bitaxeorg/BitaxeGammaHex/3d/TSOT-23-5_RIT.step

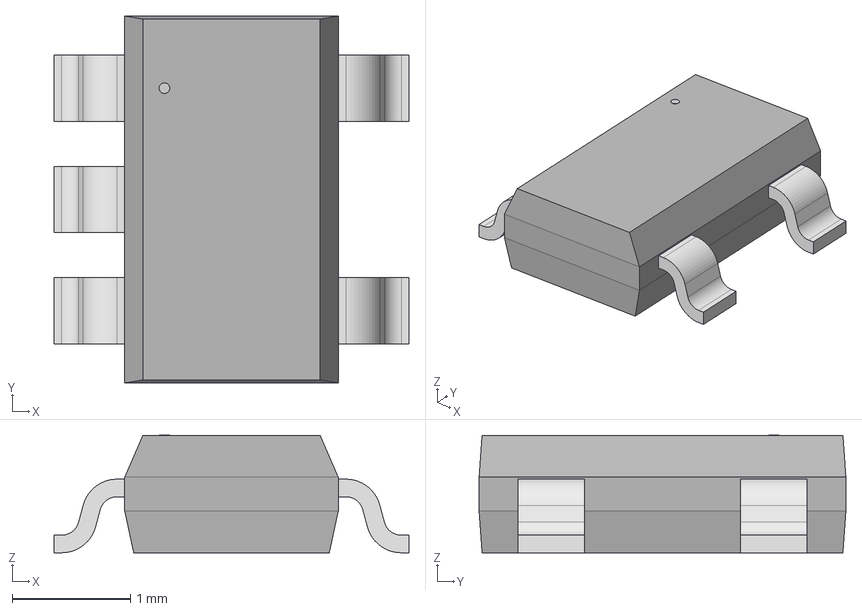
[picture p17: CAD file, 2026-07-20]
3d/TSOT-23-5_RIT.step
3.00 x 3.10 x 0.993 mm
