bitaxeorg/BitaxeGammaHex/3d/DRC0010J.stp

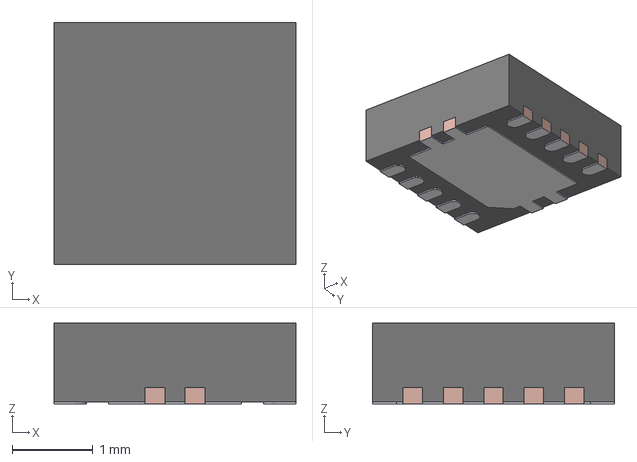
[picture p18: CAD file, 2026-07-20]
3d/DRC0010J.stp
3.00 x 3.00 x 1.00 mm
BODY-SON
FRAME-DRC0010J
