bitaxeorg/BitaxeGammaHex/3d/XTAL_SC32S-7PF20PPM_EPS.step

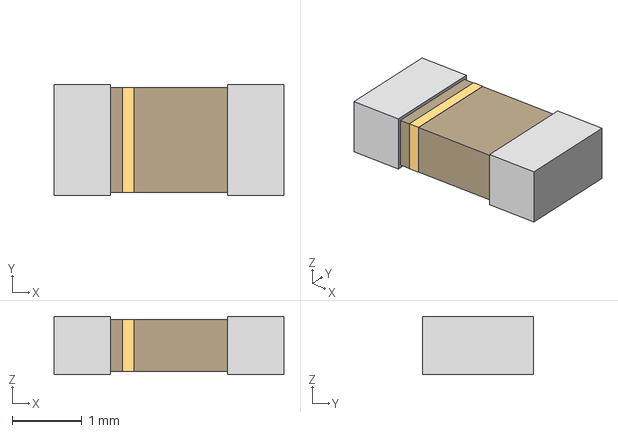
[picture p19: CAD file, 2026-07-20]
3d/XTAL_SC32S-7PF20PPM_EPS.step
3.30 x 1.60 x 0.838 mm
