bitaxeorg/BitaxeGammaHex/3d/BQB0016A.stp

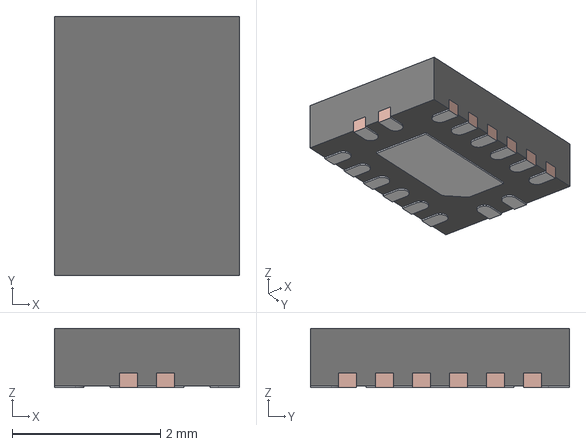
[picture p20: CAD file, 2026-07-20]
3d/BQB0016A.stp
2.50 x 3.50 x 0.8 mm
FRAME
