bitaxeorg/BitaxeGammaHex/3d/SOT-23-5_M5_MCH.step

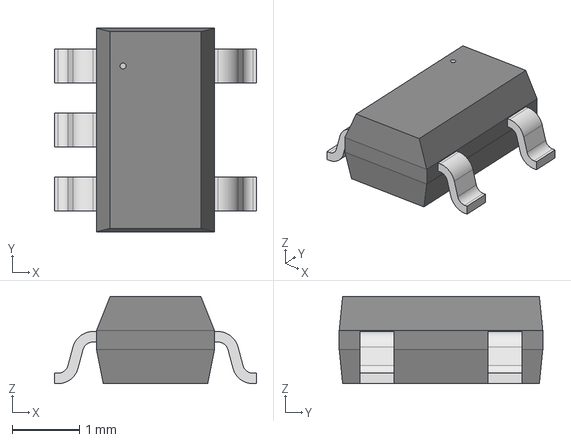
[picture p22: CAD file, 2026-07-20]
3d/SOT-23-5_M5_MCH.step
3.00 x 3.02 x 1.30 mm
