bitaxeorg/BitaxeGammaHex/3d/Bitaxe_Heatsink.step

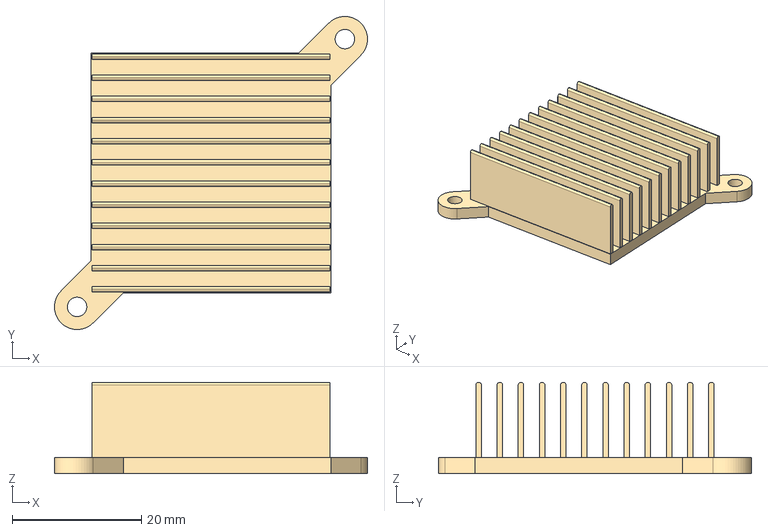
[picture p24: CAD file, 2026-07-20]
3d/Bitaxe_Heatsink.step
48.4 x 48.4 x 14.1 mm
