bitaxeorg/BitaxeGammaHex/3d/oscillator3.2x2.5.step

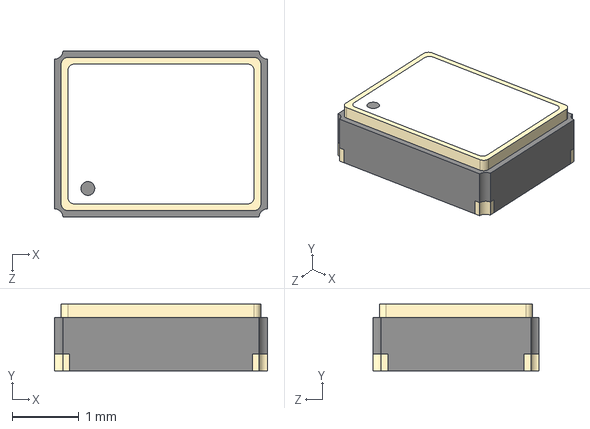
[picture p25: CAD file, 2026-07-20]
3d/oscillator3.2x2.5.step
3.20 x 1.00 x 2.50 mm
