bitaxeorg/BitaxeGammaHex/3d/c-63862-1-r-3d.stp

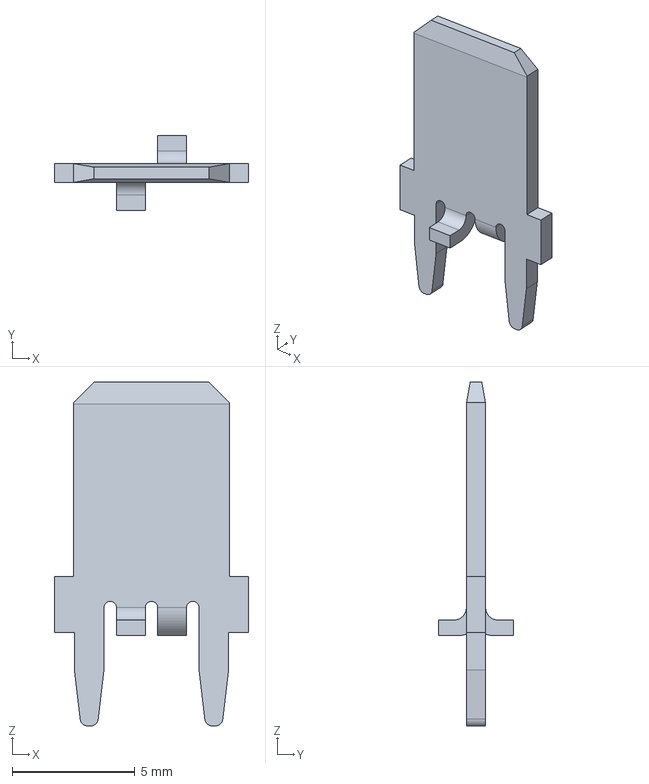
[picture p26: CAD file, 2026-07-20]
3d/c-63862-1-r-3d.stp
7.92 x 3.07 x 14.0 mm
