bitaxeorg/BitaxeGammaHex/3d/CS1213AG-tr.stp

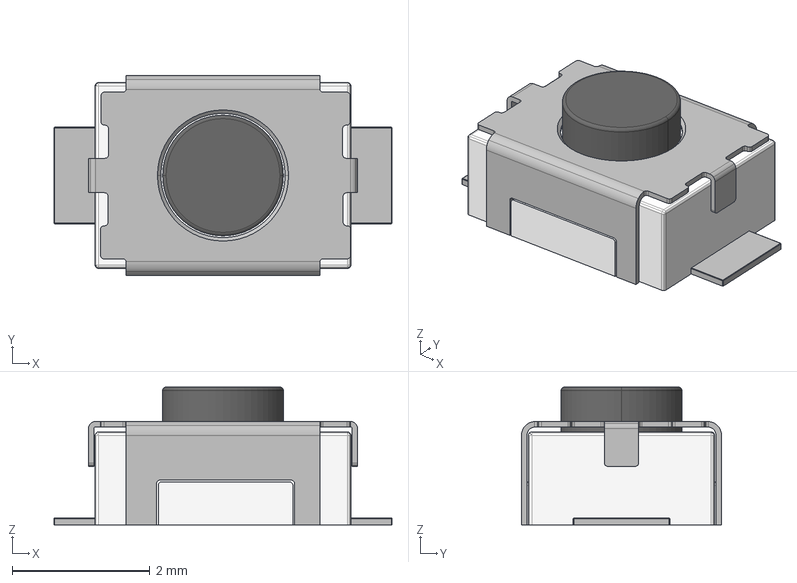
[picture p28: CAD file, 2026-07-20]
3d/CS1213AG-tr.stp
4.90 x 2.90 x 2.00 mm
