bitaxeorg/BitaxeGammaHex/3d/lga115x.step

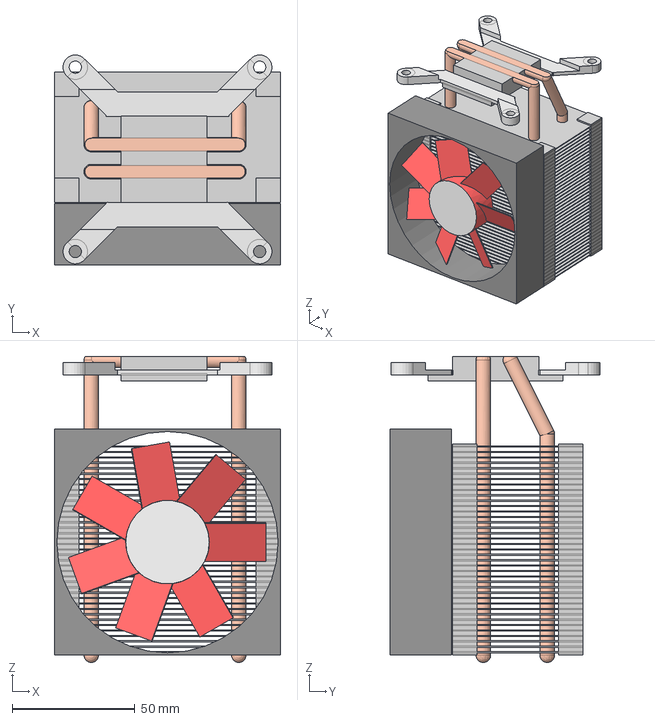
[picture p29: CAD file, 2026-07-20]
3d/lga115x.step
92.0 x 85.5 x 124.5 mm
