bitaxeorg/BitaxeGammaHex/3d/OLED_0.91_128x32.stp

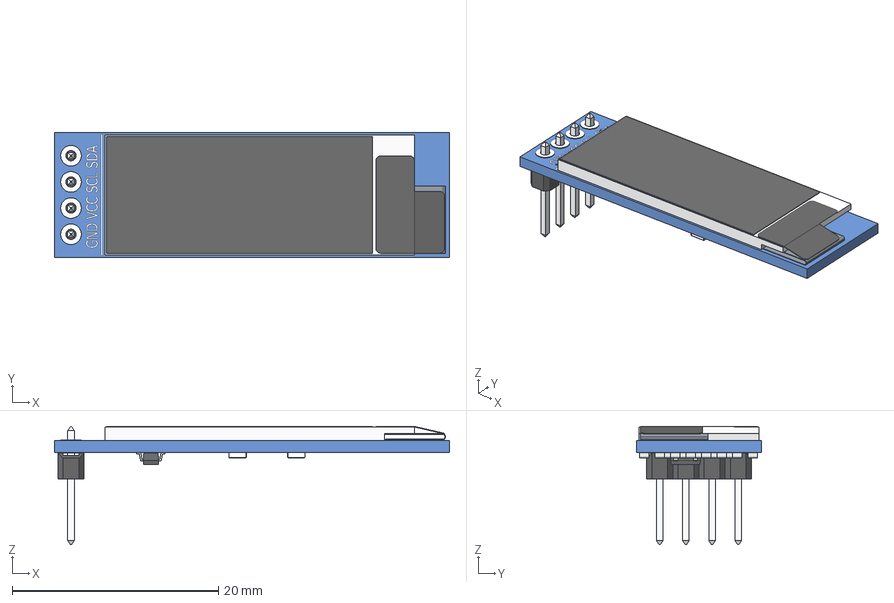
[picture p30: CAD file, 2026-07-20]
3d/OLED_0.91_128x32.stp
38.3 x 12.1 x 11.5 mm
OLED_0.91_128x32
Pin Header 4 x 1 TH 2.54mm Pitch
RESC-0603 x 13
2SD0601A
