bitaxeorg/BitaxeGammaHex/3d/CX3225SB16000H0FLJCC.STEP

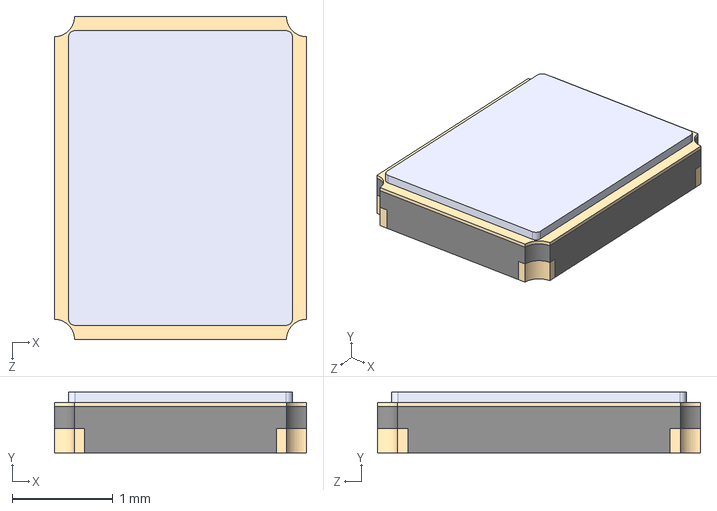
[picture p31: CAD file, 2026-07-20]
3d/CX3225SB16000H0FLJCC.STEP
2.50 x 0.6 x 3.20 mm
