bitaxeorg/BitaxeGammaHex/3d/bm1366.step

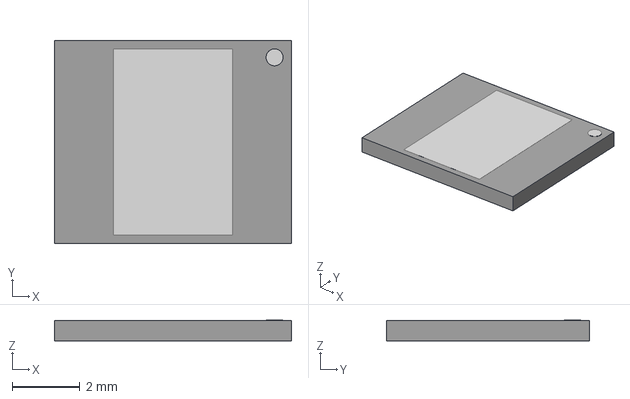
[picture p32: CAD file, 2026-07-20]
3d/bm1366.step
7.00 x 6.00 x 0.61 mm
