bitaxeorg/BitaxeGammaHex/3d/barrel-jack.step

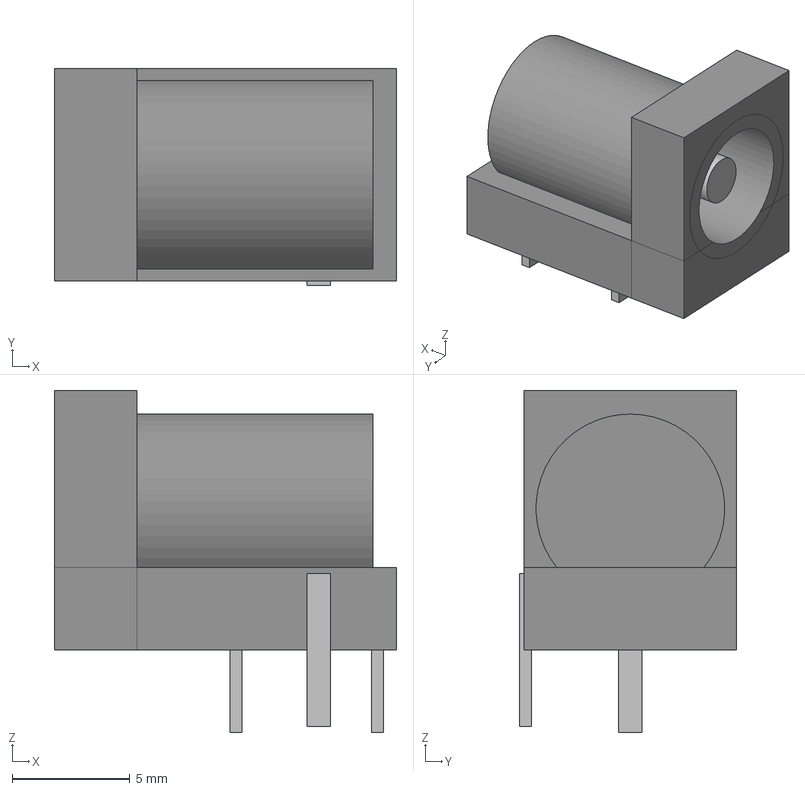
[picture p33: CAD file, 2026-07-20]
3d/barrel-jack.step
14.5 x 9.20 x 14.5 mm
