bitaxeorg/BitaxeGammaHex/3d/SN74AXC1T45DBVR.STEP

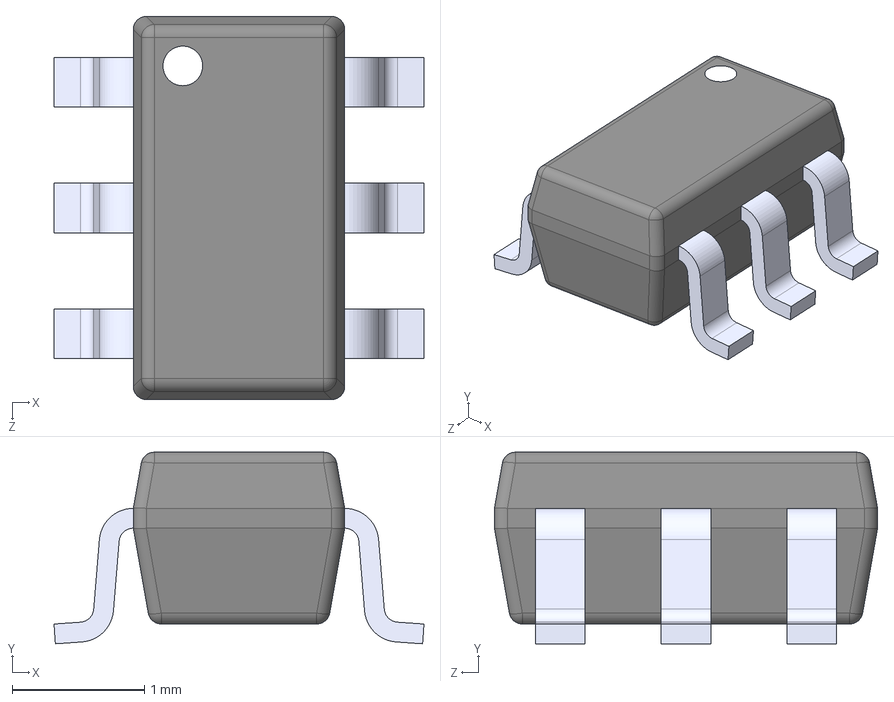
[picture p34: CAD file, 2026-07-20]
3d/SN74AXC1T45DBVR.STEP
2.80 x 1.45 x 2.90 mm
