bitaxeorg/BitaxeGammaHex/3d/heatsink-13x12x5.step

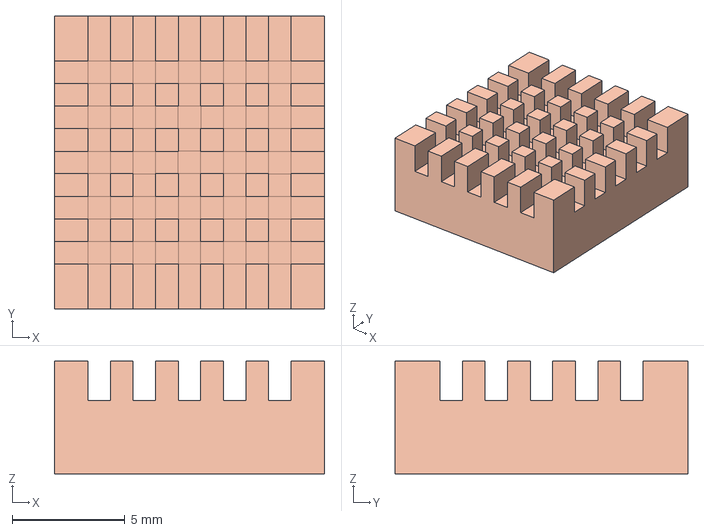
[picture p37: CAD file, 2026-07-20]
3d/heatsink-13x12x5.step
12.0 x 13.0 x 5.00 mm
