bitaxeorg/BitaxeGammaHex/3d/KMR231GLFS.stp

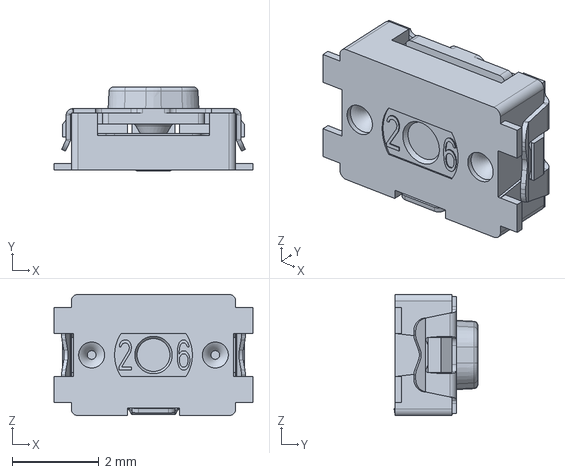
[picture p38: CAD file, 2026-07-20]
3d/KMR231GLFS.stp
4.60 x 1.94 x 2.80 mm
