bitaxeorg/BitaxeGammaHex/3d/21-0164B_L622-1_MXM.step

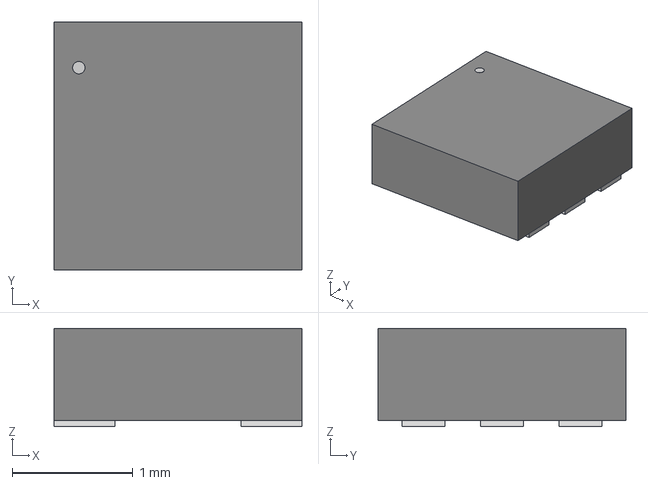
[picture p40: CAD file, 2026-07-20]
3d/21-0164B_L622-1_MXM.step
2.06 x 2.06 x 0.815 mm
