bitaxeorg/BitaxeGammaHex/3d/CUI_DEVICES_PJ-002AH.step

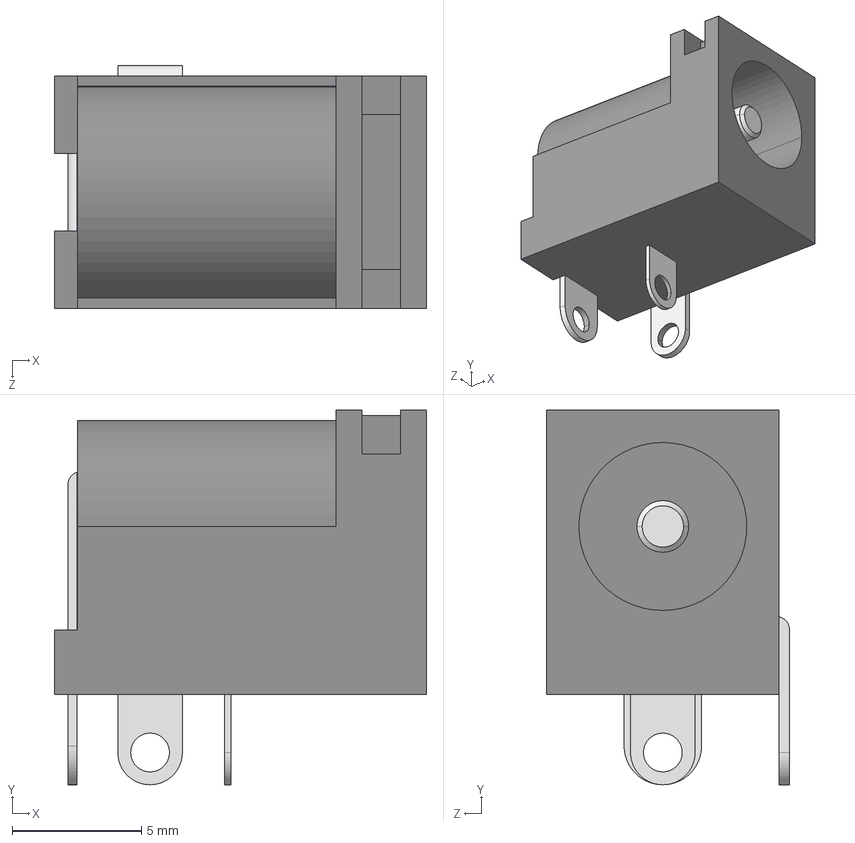
[picture p42: CAD file, 2026-07-20]
3d/CUI_DEVICES_PJ-002AH.step
14.4 x 14.5 x 9.40 mm
