bitaxeorg/BitaxeGammaHex/3d/CUI_DEVICES_PJ-037AH.step

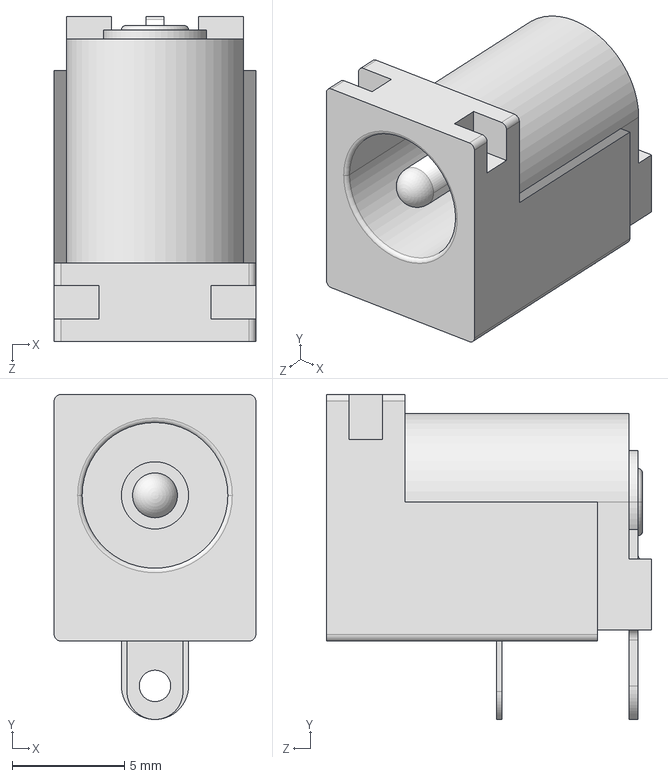
[picture p43: CAD file, 2026-07-20]
3d/CUI_DEVICES_PJ-037AH.step
9.00 x 14.5 x 14.5 mm
