bitaxeorg/BitaxeGammaHex/3d/SMV_z90.stp

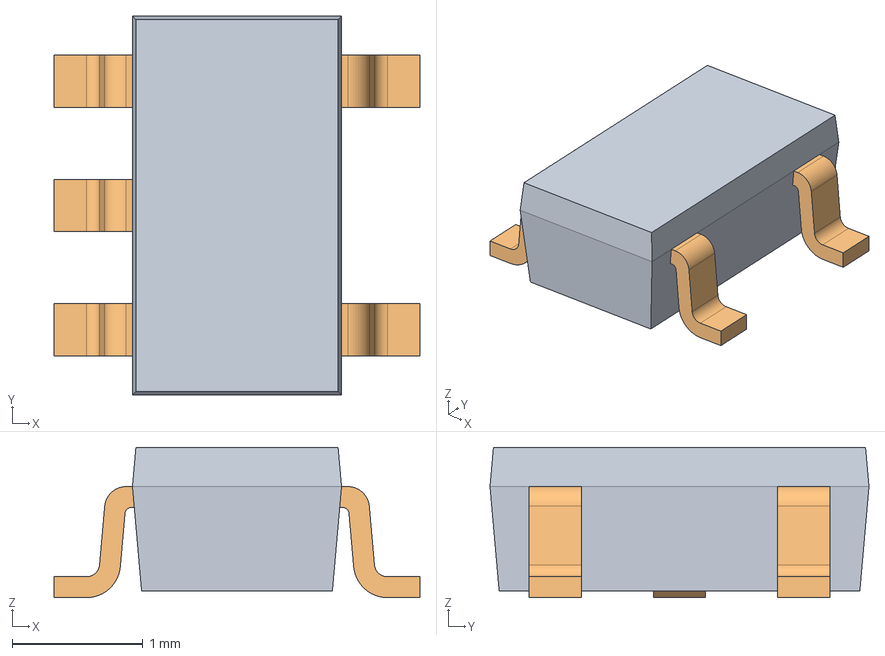
[picture p45: CAD file, 2026-07-20]
3d/SMV_z90.stp
2.80 x 2.90 x 1.15 mm
