bitaxeorg/BitaxeGammaHex/3d/XRCGB27M120F3M10R0_MUR.step

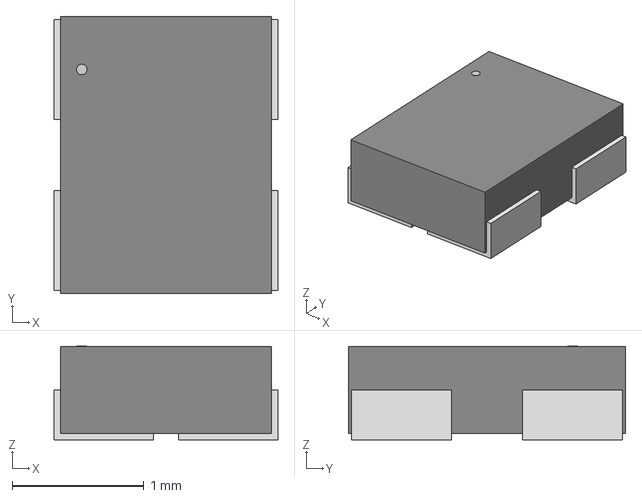
[picture p46: CAD file, 2026-07-20]
3d/XRCGB27M120F3M10R0_MUR.step
1.70 x 2.11 x 0.714 mm
