bitaxeorg/BitaxeGammaHex/3d/XT30PW-M.stp

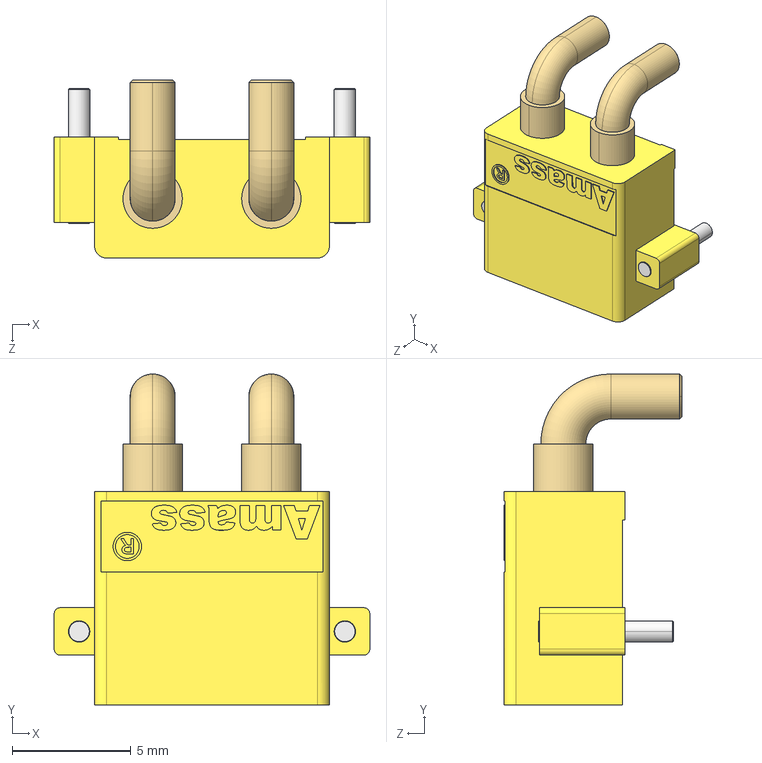
[picture p48: CAD file, 2026-07-20]
3d/XT30PW-M.stp
13.3 x 13.9 x 7.50 mm
