bitaxeorg/BitaxeGammaHex/3d/bm1370.step

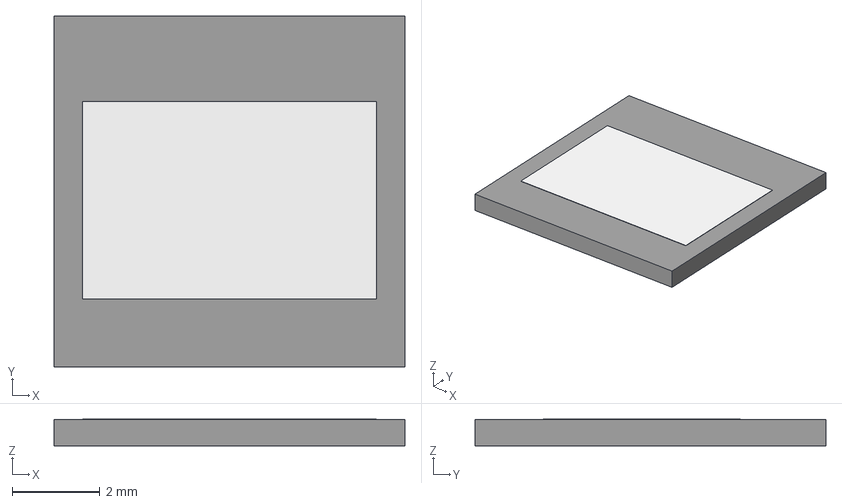
[picture p49: CAD file, 2026-07-20]
3d/bm1370.step
8.00 x 8.00 x 0.61 mm
