bitaxeorg/BitaxeGammaHex/3d/DCJ250-20-B-XX-X_REVA1.step

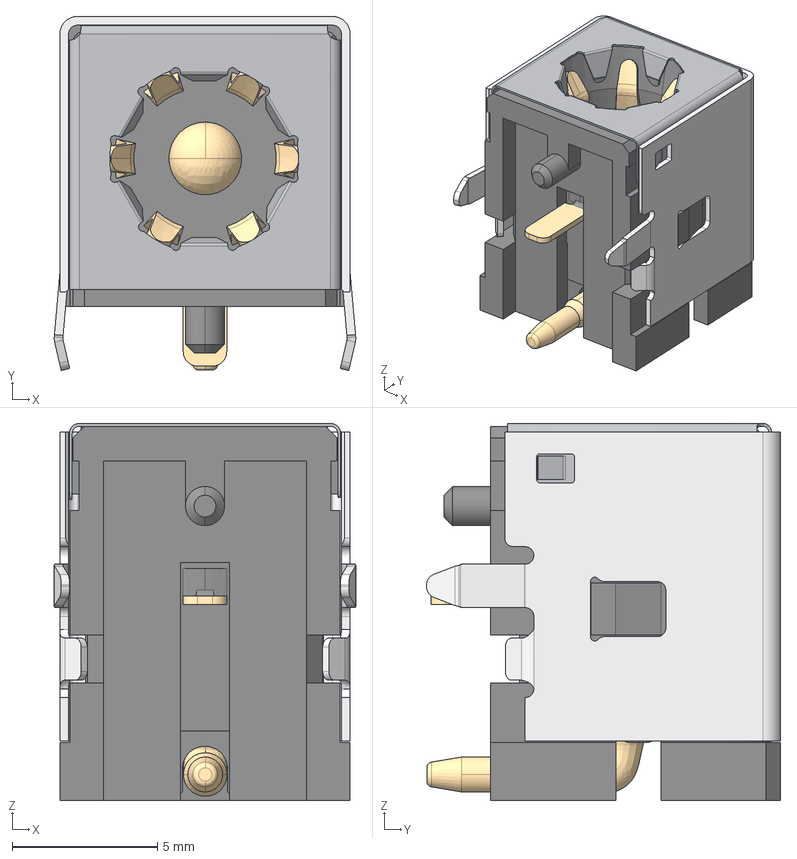
[picture p51: CAD file, 2026-07-20]
3d/DCJ250-20-B-XX-X_REVA1.step
10.4 x 12.2 x 13.0 mm
