bitaxeorg/BitaxeGammaHex/3d/SIS0011A.stp

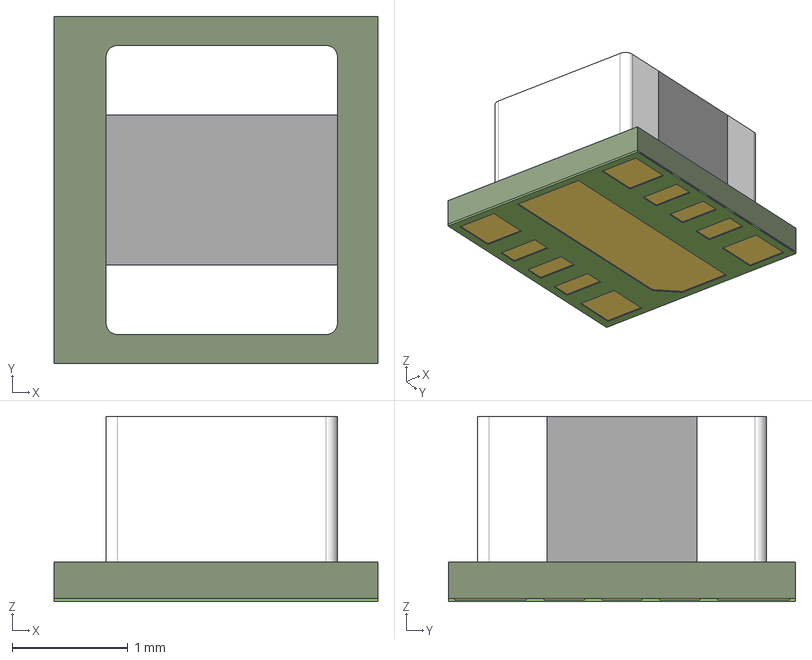
[picture p52: CAD file, 2026-07-20]
3d/SIS0011A.stp
2.80 x 3.00 x 1.60 mm
SOLDERMASK-SIS0011A
METAL-SIS0011A
SUBSTRATE-SIP
INDUCTOR-BODY-MLV
INDUCTOR-TERMNL-MLV x 2
