bitaxeorg/BitaxeGammaHex/3d/PLCC6_LED_3_5X3_4X2_8_CRW.step

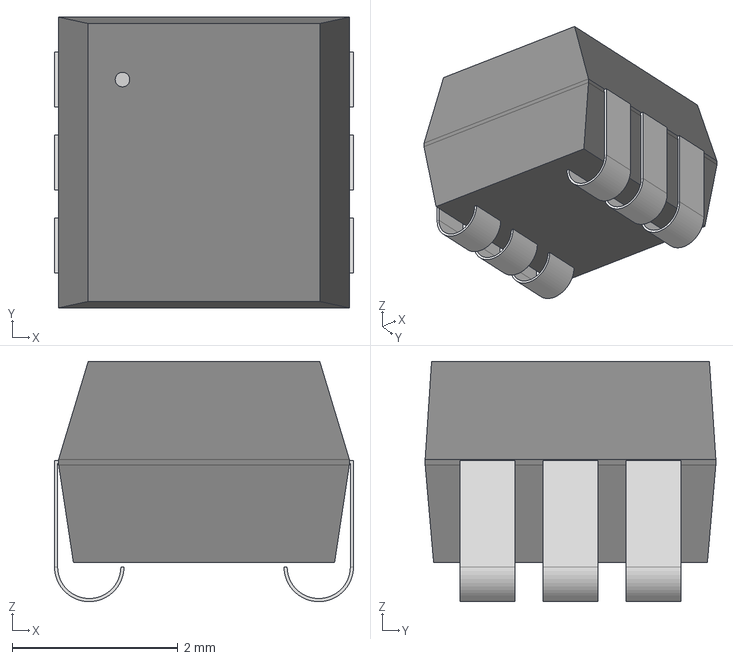
[picture p53: CAD file, 2026-07-20]
3d/PLCC6_LED_3_5X3_4X2_8_CRW.step
3.61 x 3.51 x 2.90 mm
