bitaxeorg/BitaxeGammaHex/3d/SW_CS1213AGF260_CRS.step

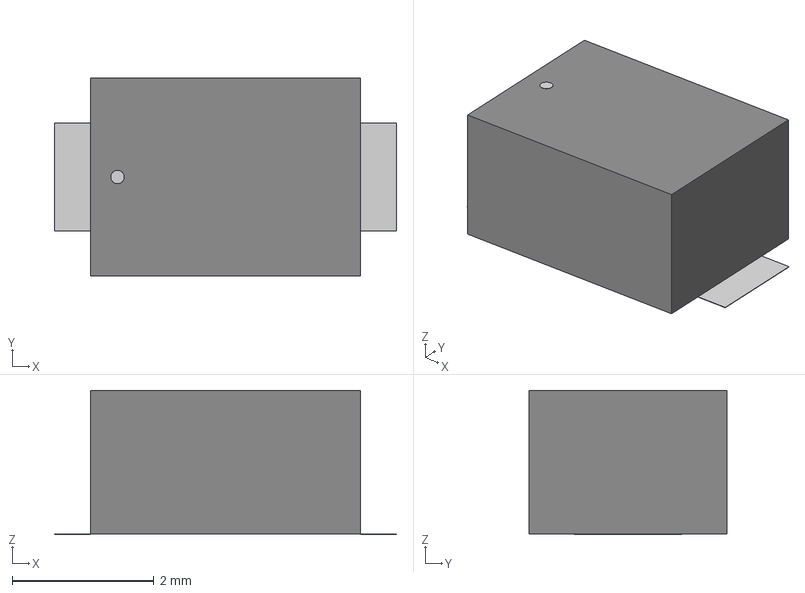
[picture p54: CAD file, 2026-07-20]
3d/SW_CS1213AGF260_CRS.step
4.83 x 2.79 x 2.04 mm
