bitaxeorg/BitaxeGammaHex/3d/Coilcraft-SLC1175.STEP

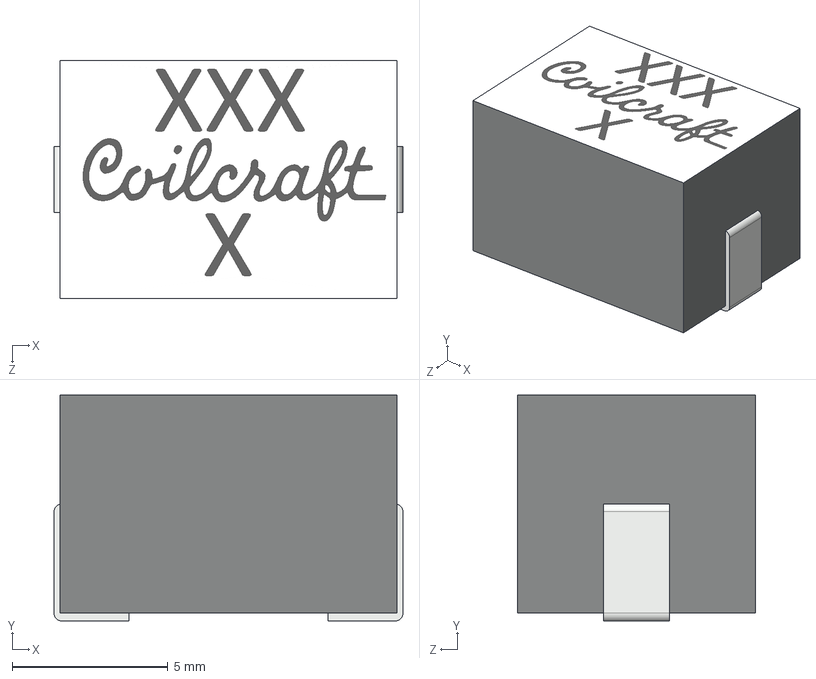
[picture p55: CAD file, 2026-07-20]
3d/Coilcraft-SLC1175.STEP
11.2 x 7.25 x 7.65 mm
