bitaxeorg/BitaxeGammaHex/BitaxeGammaHex.kicad_sch

## KiCad design BitaxeGammaHex.kicad_sch (2026-07-27)

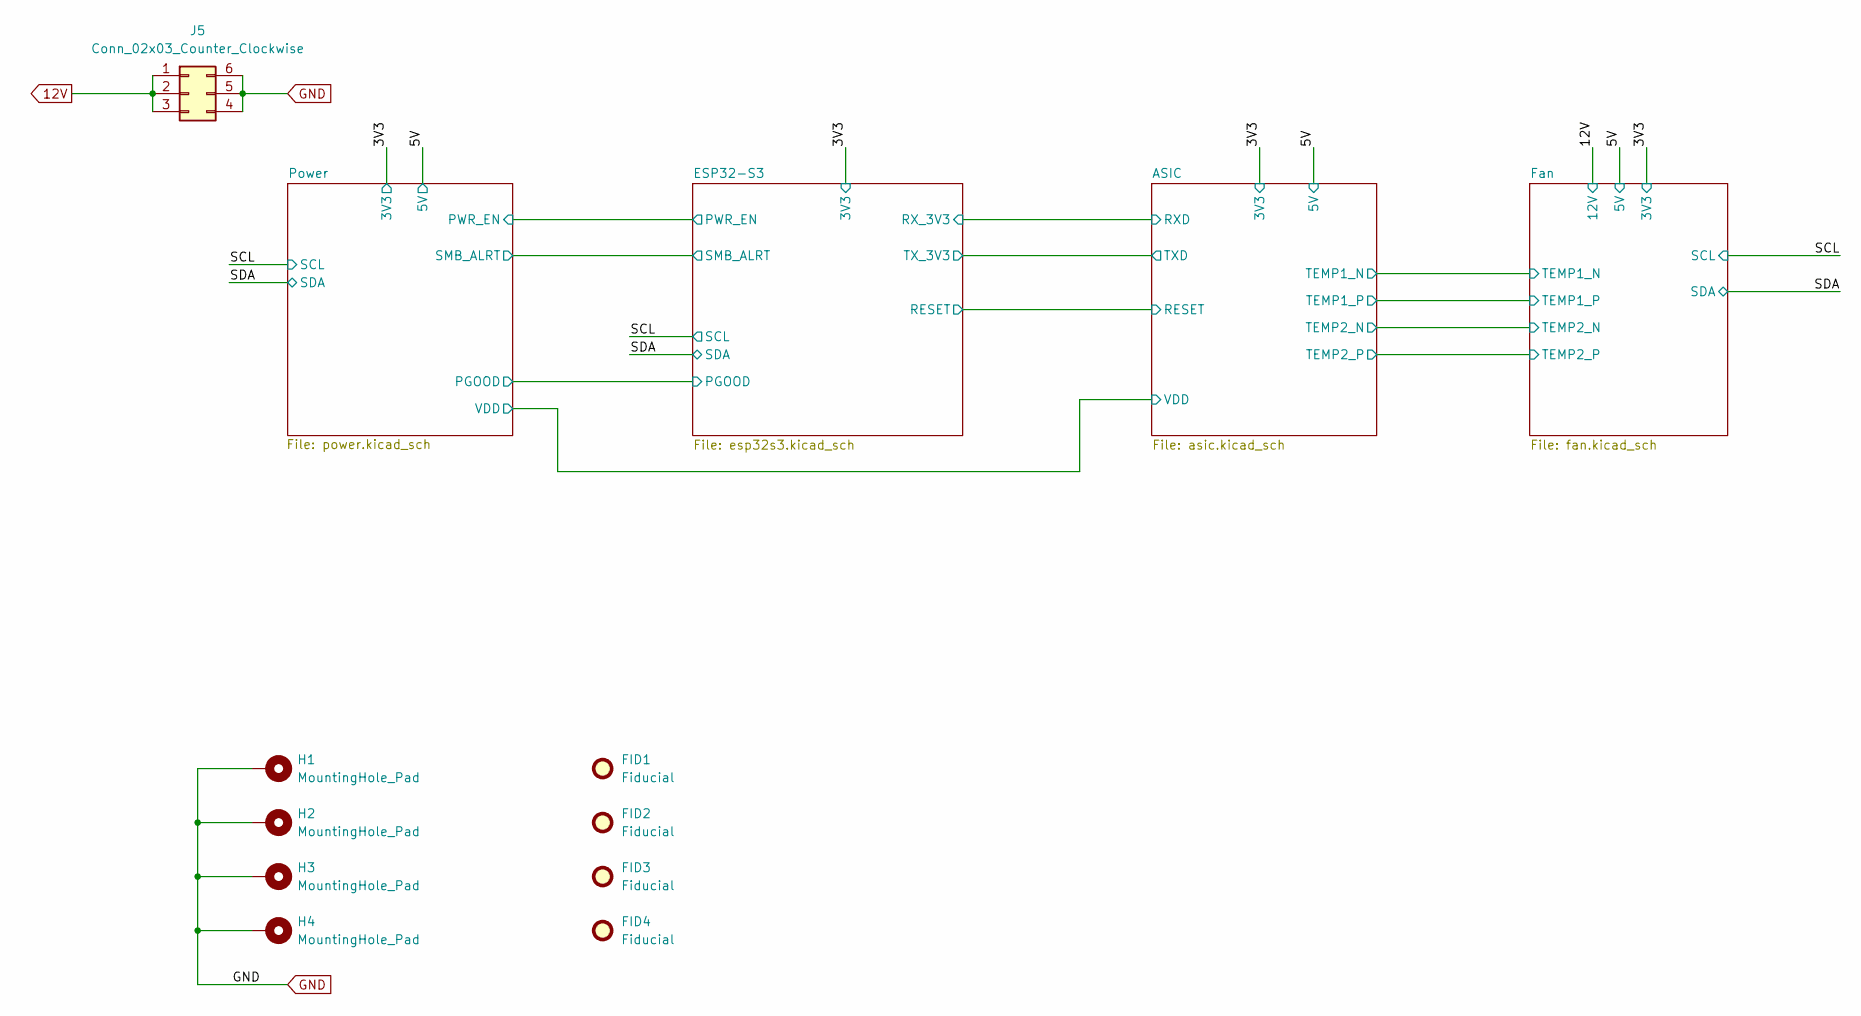
[picture p56: schematic BitaxeGammaHex.kicad_sch]

Parts:
FID1, FID2, FID3, FID4: Fiducial; Fiducial_1mm_Mask2mm
H1, H2, H3, H4: MountingHole_Pad; MountingHole_3.2mm_M3_Pad_Via
J5: Conn_02x03_Counter_Clockwise; MOLEX 39301060

Connections:
12V: J5.1, J5.2, J5.3
GND: H1.1, H2.1, H3.1, H4.1, J5.4, J5.5, J5.6
