bitaxeorg/BitaxeGammaHex/asic.kicad_sch

## KiCad design asic.kicad_sch (2026-07-27)

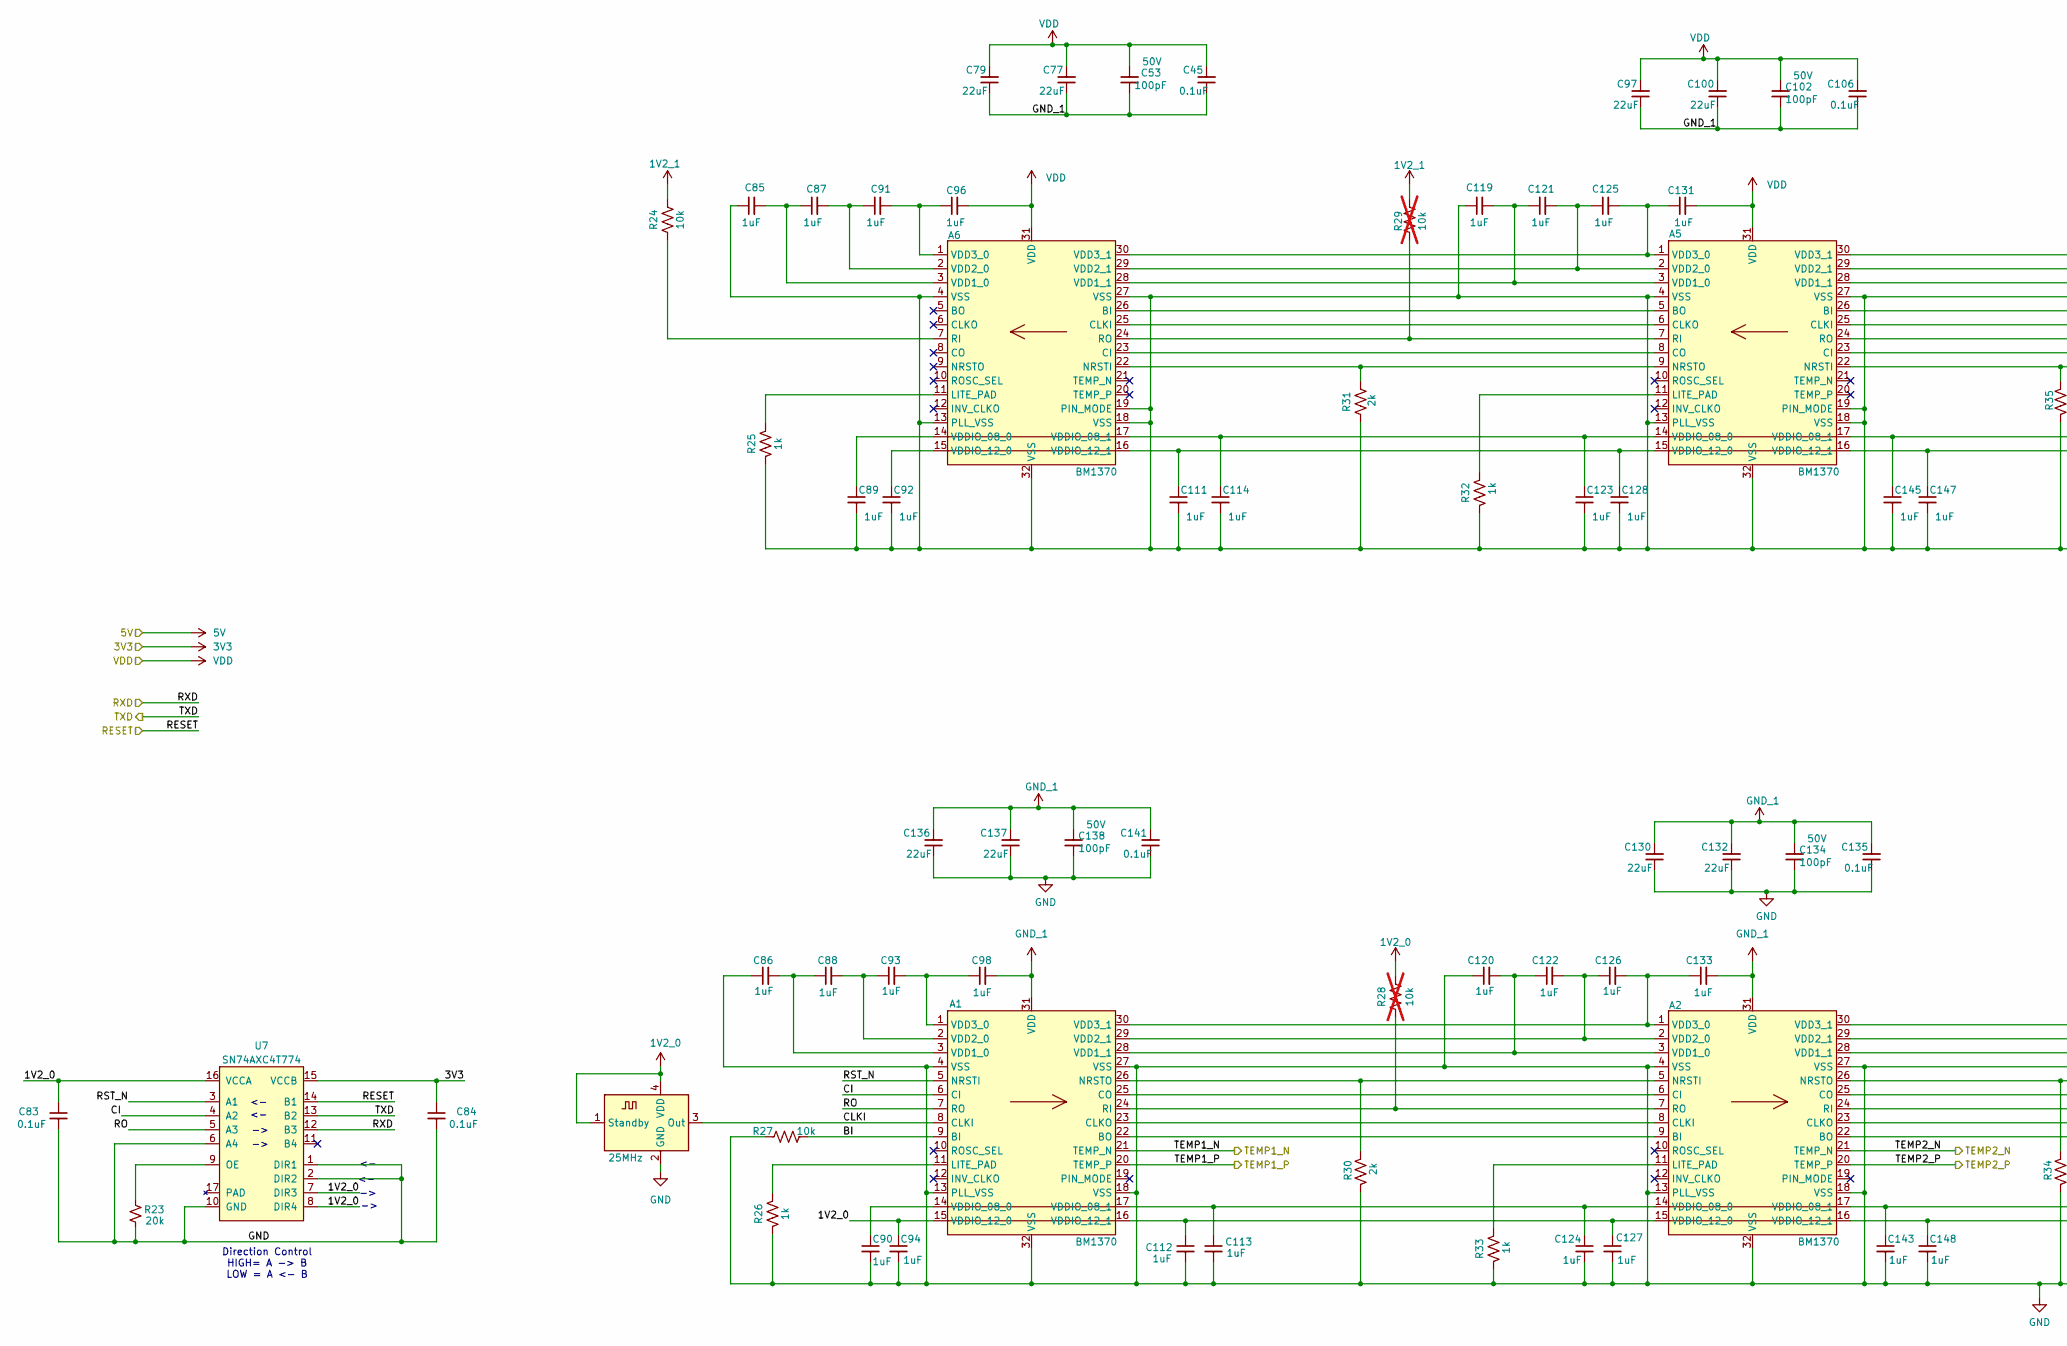
[picture p57: schematic asic.kicad_sch, part in row 1, column 1]

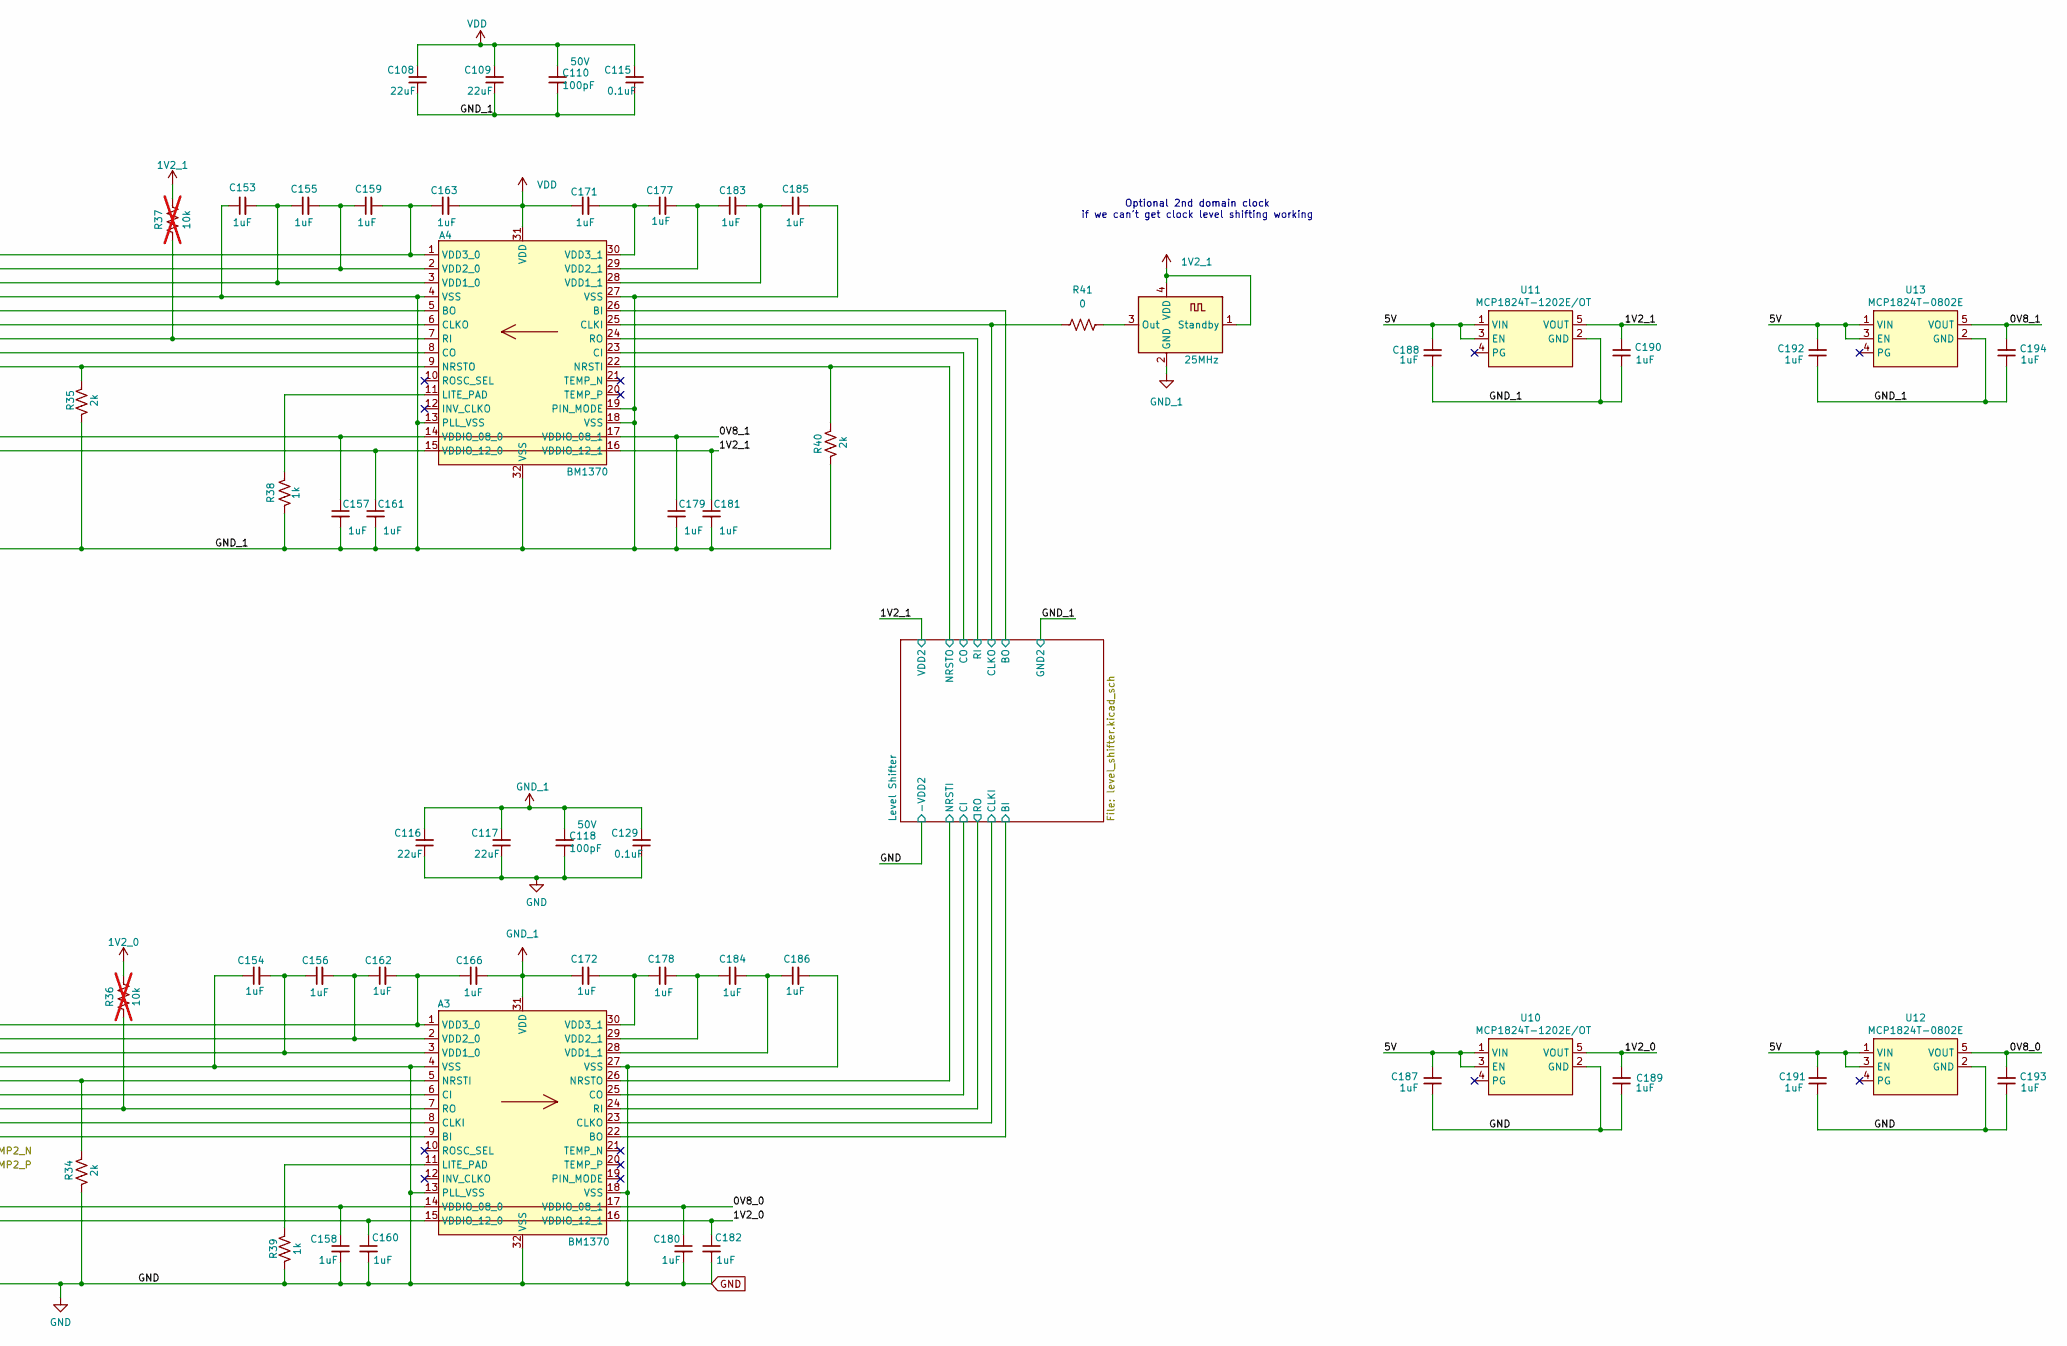
[picture p58: schematic asic.kicad_sch, part in row 1, column 2]

Parts:
A1, A2, A3, A4, A5, A6: BM1370; PARTNO BM1370
C45, C106, C115, C129, C135, C141: 0.1uF; C_0402_1005Metric; PARTNO GRM188R61E106KA73D
C53, C102, C110, C118, C134, C138: 100pF; C_0402_1005Metric; Voltage 50V; PARTNO CC0402JRNPO9BN101
C77, C79, C97, C100, C108, C109, C116, C117, C130, C132, C136, C137: 22uF; C_0805_2012Metric; PARTNO CL21A226MAQNNNE
C83, C84: 0.1uF; C_0402_1005Metric; PARTNO KGM05AR71C104KH
C85, C86, C87, C88, C89, C90, C91, C92, C93, C94, C96, C98, C111, C112, C113, C114, C119, C120, C121, C122, C123, C124, C125, C126, C127, C128, C131, C133, C143, C145, C147, C148, C153, C154, C155, C156, C157, C158, C159, C160, C161, C162, C163, C166, C171, C172, C177, C178, C179, C180, C181, C182, C183, C184, C185, C186: 1uF; C_0402_1005Metric; PARTNO CL05A105KO5NNNC; LCSC C29266
C187, C188, C189, C190, C191, C192, C193, C194: 1uF; C_0402_1005Metric; PARTNO CL05A105KO5NNNC
R23: 20k; R_0402_1005Metric; PARTNO RC0402FR-0720KL
R24, R27: 10k; R_0402_1005Metric; PARTNO RC0402DR-0710KL; LCSC C471764
R25, R26, R32, R33, R38, R39: 1k; R_0402_1005Metric; PARTNO RC0402FR-071KL; LCSC C106235
R28, R29, R36, R37: 10k; R_0402_1005Metric; PARTNO RC0402DR-0710KL; LCSC C471764; not fitted
R30, R31, R34, R35, R40: 2k; R_0402_1005Metric; PARTNO RC0402FR-072KL; LCSC C60488
R41: 0; R_0402_1005Metric; PARTNO RC0402JR-070RL
U7: SN74AXC4T774; TSSOP-16_4.4x5mm_P0.65mm; PARTNO SN74AXC4T774PWR
U8, U9: 25MHz; Oscillator_SMD_EuroQuartz_XO32-4Pin_3.2x2.5mm; PARTNO SX3M25.000E20F30THN
U10, U11: MCP1824T-1202E/OT; SOT-23-5; PARTNO MCP1824T-1202E/OT
U12, U13: MCP1824T-0802E; SOT-23-5; PARTNO MCP1824T-0802E/OT

Connections:
0V8_0: A3.17 (VDDIO_08_1), C180.1, C193.2, U12.5 (VOUT)
0V8_1: A4.17 (VDDIO_08_1), C179.1, C194.2, U13.5 (VOUT)
1V2_0: A1.15 (VDDIO_12_0), A3.16 (VDDIO_12_1), C83.1, C94.1, C182.1, C189.2, R28.2, R36.2, U7.7 (DIR3), U7.8 (DIR4), U7.16 (VCCA), U8.1 (Standby), U8.4 (VDD), U10.5 (VOUT)
1V2_1: A4.16 (VDDIO_12_1), C181.1, C190.2, R24.2, R29.2, R37.2, U9.1 (Standby), U9.4 (VDD), U11.5 (VOUT)
3V3: C84.1, U7.15 (VCCB)
5V: C187.2, C188.2, C191.2, C192.2, U10.1 (VIN), U10.3 (EN), U11.1 (VIN), U11.3 (EN), U12.1 (VIN), U12.3 (EN), U13.1 (VIN), U13.3 (EN)
BI: A1.9 (BI), A3.22 (BO), R27.2
BO: A4.26 (BI)
CI: A1.6 (CI), A3.25 (CO), U7.4 (A2)
CLKI: A1.8 (CLKI), A3.23 (CLKO), U8.3 (Out)
CLKO: A4.25 (CLKI), R41.1
CO: A4.23 (CI)
GND: A1.4 (VSS), A1.13 (PLL_VSS), A1.18 (VSS), A1.27 (VSS), A1.32 (VSS), A2.4 (VSS), A2.13 (PLL_VSS), A2.18 (VSS), A2.27 (VSS), A2.32 (VSS), A3.4 (VSS), A3.13 (PLL_VSS), A3.18 (VSS), A3.27 (VSS), A3.32 (VSS), C83.2, C84.2, C86.1, C90.2, C94.2, C112.2, C113.2, C116.1, C117.1, C118.1, C120.1, C124.2, C127.2, C129.1, C130.1, C132.1, C134.1, C135.1, C136.1, C137.1, C138.1, C141.1, C143.2, C148.2, C154.1, C158.2, C160.2, C180.2, C182.2, C186.2, C187.1, C189.1, C191.1, C193.1, R23.1, R26.2, R27.1, R30.1, R33.2, R34.1, R39.2, U7.1 (DIR1), U7.2 (DIR2), U7.6 (A4), U7.10 (GND), U8.2 (GND), U10.2 (GND), U12.2 (GND)
GND_1: A1.31 (VDD), A2.31 (VDD), A3.31 (VDD), A4.4 (VSS), A4.13 (PLL_VSS), A4.18 (VSS), A4.19 (PIN_MODE), A4.27 (VSS), A4.32 (VSS), A5.4 (VSS), A5.13 (PLL_VSS), A5.18 (VSS), A5.19 (PIN_MODE), A5.27 (VSS), A5.32 (VSS), A6.4 (VSS), A6.13 (PLL_VSS), A6.18 (VSS), A6.19 (PIN_MODE), A6.27 (VSS), A6.32 (VSS), C45.1, C53.1, C77.1, C79.1, C85.1, C89.2, C92.2, C97.1, C98.2, C100.1, C102.1, C106.1, C108.1, C109.1, C110.1, C111.2, C114.2, C115.1, C116.2, C117.2, C118.2, C119.1, C123.2, C128.2, C129.2, C130.2, C132.2, C133.2, C134.2, C135.2, C136.2, C137.2, C138.2, C141.2, C145.2, C147.2, C153.1, C157.2, C161.2, C166.2, C172.1, C179.2, C181.2, C185.2, C188.1, C190.1, C192.1, C194.1, R25.2, R31.1, R32.2, R35.1, R38.2, R40.1, U9.2 (GND), U11.2 (GND), U13.2 (GND)
NRSTI: A3.26 (NRSTO)
NRSTO: A4.22 (NRSTI), R40.2
unnamed: A1.1 (VDD3_0), C93.2, C98.1
unnamed: A1.2 (VDD2_0), C88.2, C93.1
unnamed: A1.3 (VDD1_0), C86.2, C88.1
unnamed: A1.11 (LITE_PAD), R26.1
unnamed: A1.14 (VDDIO_08_0), C90.1
unnamed: A1.16 (VDDIO_12_1), A2.15 (VDDIO_12_0), C112.1, C127.1
unnamed: A1.17 (VDDIO_08_1), A2.14 (VDDIO_08_0), C113.1, C124.1
unnamed: A1.22 (BO), A2.9 (BI)
unnamed: A1.23 (CLKO), A2.8 (CLKI)
unnamed: A1.24 (RI), A2.7 (RO), R28.1
unnamed: A1.25 (CO), A2.6 (CI)
unnamed: A1.26 (NRSTO), A2.5 (NRSTI), R30.2
unnamed: A1.28 (VDD1_1), A2.3 (VDD1_0), C120.2, C122.1
unnamed: A1.29 (VDD2_1), A2.2 (VDD2_0), C122.2, C126.1
unnamed: A1.30 (VDD3_1), A2.1 (VDD3_0), C126.2, C133.1
unnamed: A2.11 (LITE_PAD), R33.1
unnamed: A2.16 (VDDIO_12_1), A3.15 (VDDIO_12_0), C148.1, C160.1
unnamed: A2.17 (VDDIO_08_1), A3.14 (VDDIO_08_0), C143.1, C158.1
unnamed: A2.22 (BO), A3.9 (BI)
unnamed: A2.23 (CLKO), A3.8 (CLKI)
unnamed: A2.24 (RI), A3.7 (RO), R36.1
unnamed: A2.25 (CO), A3.6 (CI)
unnamed: A2.26 (NRSTO), A3.5 (NRSTI), R34.2
unnamed: A2.28 (VDD1_1), A3.3 (VDD1_0), C154.2, C156.1
unnamed: A2.29 (VDD2_1), A3.2 (VDD2_0), C156.2, C162.1
unnamed: A2.30 (VDD3_1), A3.1 (VDD3_0), C162.2, C166.1
unnamed: A3.11 (LITE_PAD), R39.1
unnamed: A3.28 (VDD1_1), C184.2, C186.1
unnamed: A3.29 (VDD2_1), C178.2, C184.1
unnamed: A3.30 (VDD3_1), C172.2, C178.1
unnamed: A4.1 (VDD3_0), A5.30 (VDD3_1), C159.2, C163.1
unnamed: A4.2 (VDD2_0), A5.29 (VDD2_1), C155.2, C159.1
unnamed: A4.3 (VDD1_0), A5.28 (VDD1_1), C153.2, C155.1
unnamed: A4.5 (BO), A5.26 (BI)
unnamed: A4.6 (CLKO), A5.25 (CLKI)
unnamed: A4.7 (RI), A5.24 (RO), R37.1
unnamed: A4.8 (CO), A5.23 (CI)
unnamed: A4.9 (NRSTO), A5.22 (NRSTI), R35.2
unnamed: A4.11 (LITE_PAD), R38.1
unnamed: A4.14 (VDDIO_08_0), A5.17 (VDDIO_08_1), C145.1, C157.1
unnamed: A4.15 (VDDIO_12_0), A5.16 (VDDIO_12_1), C147.1, C161.1
unnamed: A4.28 (VDD1_1), C183.2, C185.1
unnamed: A4.29 (VDD2_1), C177.2, C183.1
unnamed: A4.30 (VDD3_1), C171.2, C177.1
unnamed: A5.1 (VDD3_0), A6.30 (VDD3_1), C125.2, C131.1
unnamed: A5.2 (VDD2_0), A6.29 (VDD2_1), C121.2, C125.1
unnamed: A5.3 (VDD1_0), A6.28 (VDD1_1), C119.2, C121.1
unnamed: A5.5 (BO), A6.26 (BI)
unnamed: A5.6 (CLKO), A6.25 (CLKI)
unnamed: A5.7 (RI), A6.24 (RO), R29.1
unnamed: A5.8 (CO), A6.23 (CI)
unnamed: A5.9 (NRSTO), A6.22 (NRSTI), R31.2
unnamed: A5.11 (LITE_PAD), R32.1
unnamed: A5.14 (VDDIO_08_0), A6.17 (VDDIO_08_1), C114.1, C123.1
unnamed: A5.15 (VDDIO_12_0), A6.16 (VDDIO_12_1), C111.1, C128.1
unnamed: A6.1 (VDD3_0), C91.2, C96.1
unnamed: A6.2 (VDD2_0), C87.2, C91.1
unnamed: A6.3 (VDD1_0), C85.2, C87.1
unnamed: A6.7 (RI), R24.1
unnamed: A6.11 (LITE_PAD), R25.1
unnamed: A6.14 (VDDIO_08_0), C89.1
unnamed: A6.15 (VDDIO_12_0), C92.1
unnamed: R23.2, U7.9 (OE)
unnamed: R41.2, U9.3 (Out)
RESET: U7.14 (B1)
RI: A4.24 (RO)
RO: A1.7 (RO), A3.24 (RI), U7.5 (A3)
RST_N: A1.5 (NRSTI), U7.3 (A1)
RXD: U7.12 (B3)
TEMP1_N: A1.21 (TEMP_N)
TEMP1_P: A1.20 (TEMP_P)
TEMP2_N: A2.21 (TEMP_N)
TEMP2_P: A2.20 (TEMP_P)
TXD: U7.13 (B2)
VDD: A4.31 (VDD), A5.31 (VDD), A6.31 (VDD), C45.2, C53.2, C77.2, C79.2, C96.2, C97.2, C100.2, C102.2, C106.2, C108.2, C109.2, C110.2, C115.2, C131.2, C163.2, C171.1

Notes on the sheet:
Direction Control HIGH= A -> B LOW = A <- B
Optional 2nd domain clock if we can't get clock level shifting working
