bitaxeorg/BitaxeGammaHex/esp32s3.kicad_sch

## KiCad design esp32s3.kicad_sch (2026-07-27)

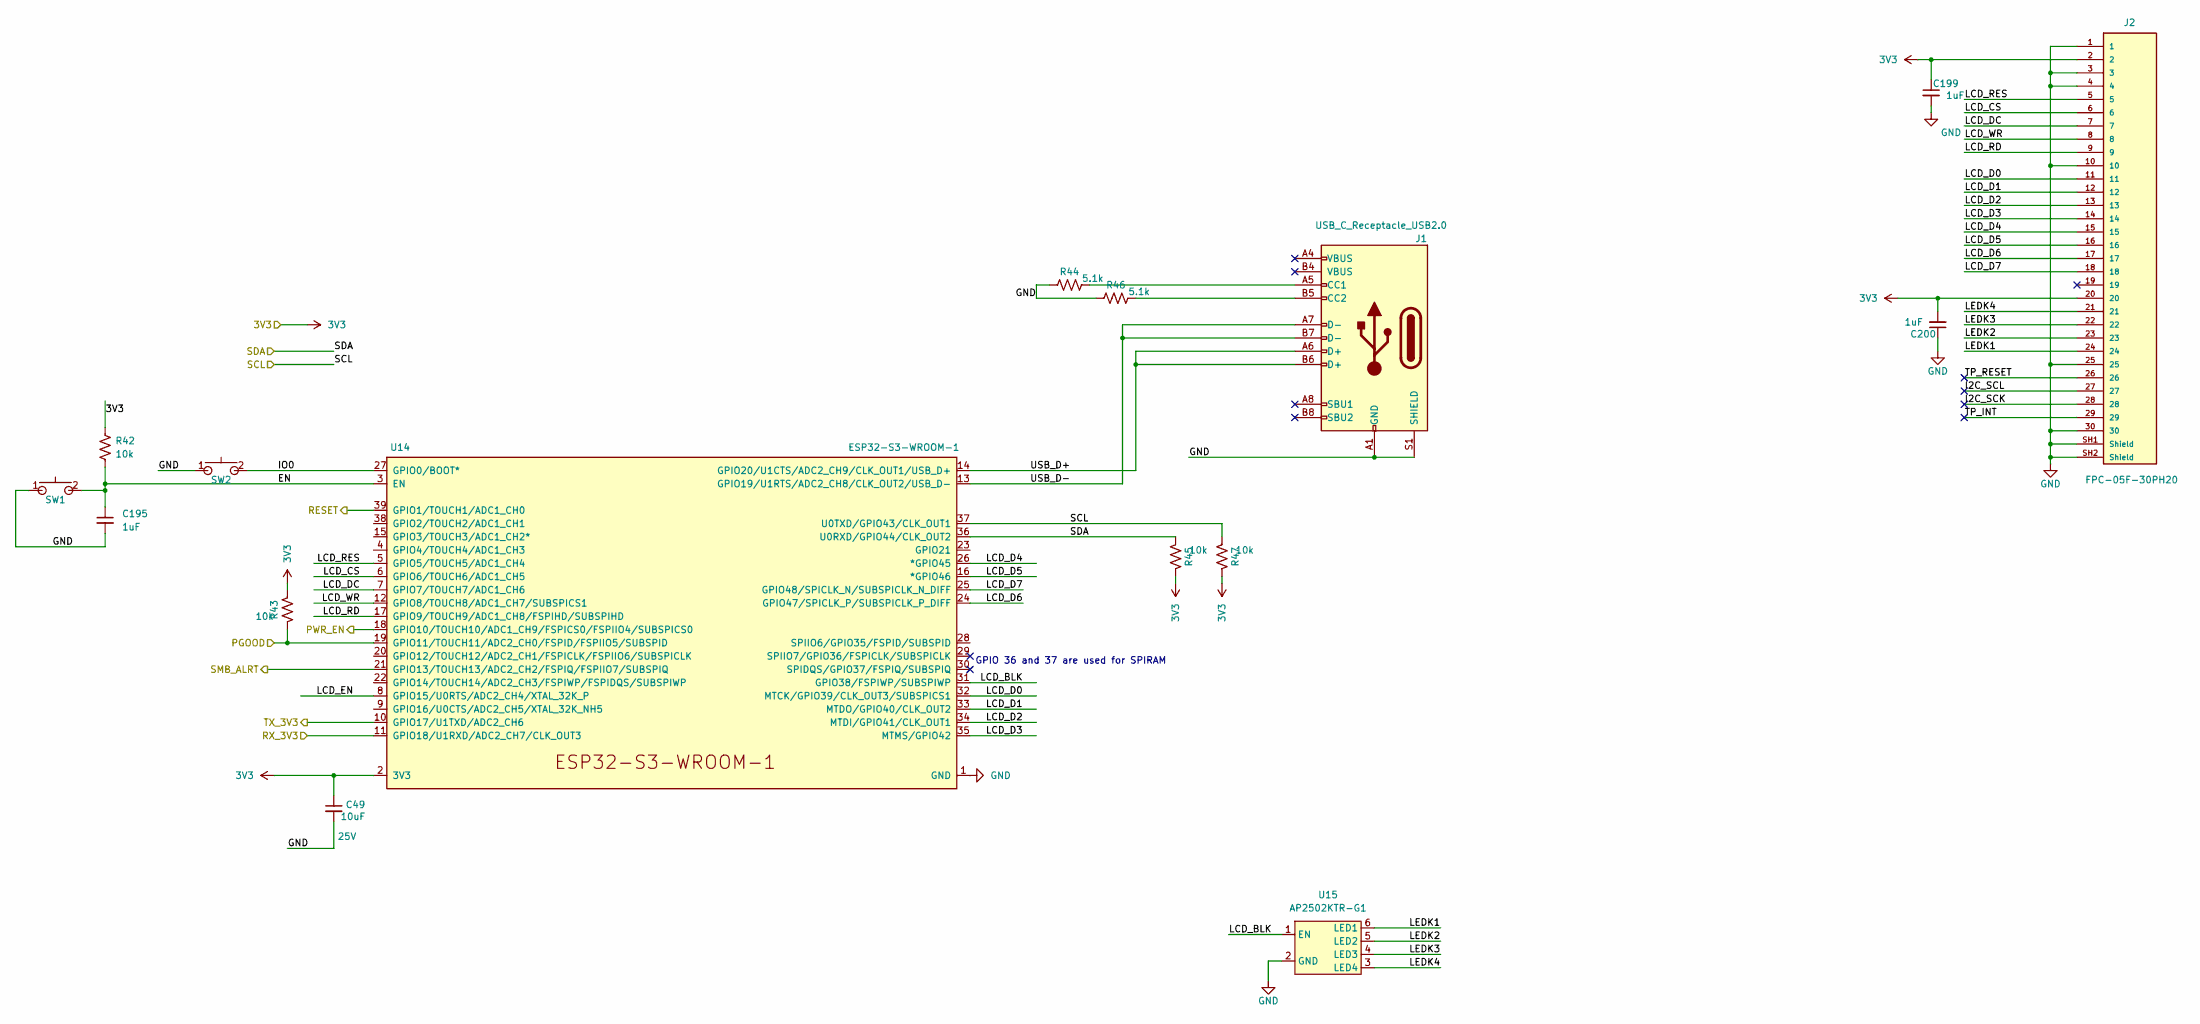
[picture p59: schematic esp32s3.kicad_sch]

Parts:
C49: 10uF; C_0603_1608Metric; Voltage 25V; PARTNO GRM188R61E106KA73D
C195, C199, C200: 1uF; C_0402_1005Metric; PARTNO CL05A105KO5NNNC
J1: USB_C_Receptacle_USB2.0; USB_C_Receptacle_GCT_USB4105-xx-A; PARTNO USB4105-GF-A
J2: FPC-05F-30PH20; FPC-SMD_30P-P0.50_XUNPU_FPC-05F-30PH20; PARTNO FPC-05FB-30PH20
R42: 10k; R_0402_1005Metric; PARTNO RC0402DR-0710KL
R43, R45, R47: 10k; R_0402_1005Metric; PARTNO RC0402DR-0710KL; LCSC C471764
R44, R46: 5.1k; R_0402_1005Metric; PARTNO RMCF0402JT5K10; LCSC Part C25905
SW1, SW2: SWITCH-SPST; SW_TL3330AF130QG_EWI; PARTNO TL3330AF130QG
U14: ESP32-S3-WROOM-1; PARTNO ESP32-S3-WROOM-1-N16R8
U15: AP2502KTR-G1; SOT-23-6; PARTNO AP2502KTR-G1

Connections:
3V3: C49.1, C199.1, C200.2, J2.2, J2.20, R42.1, R43.1, R45.1, R47.1, U14.2 (3V3)
EN: C195.1, R42.2, SW1.2, U14.3 (EN)
GND: C49.2, C195.2, C199.2, C200.1, J1.A1 (GND), J1.B1 (GND), J1.S1 (SHIELD), J2.1, J2.3, J2.4, J2.10, J2.25, J2.30, J2.SH1 (Shield), J2.SH2 (Shield), R44.1, R46.1, SW1.1, SW2.1, U14.1 (GND), U14.40 (GND), U14.41 (GND), U15.2 (GND)
I2C_SCK: J2.28
I2C_SCL: J2.27
IO0: SW2.2, U14.27 (GPIO0/BOOT*)
LCD_BLK: U14.31 (GPIO38/FSPIWP/SUBSPIWP), U15.1 (EN)
LCD_CS: J2.6, U14.6 (GPIO6/TOUCH6/ADC1_CH5)
LCD_D0: J2.11, U14.32 (MTCK/GPIO39/CLK_OUT3/SUBSPICS1)
LCD_D1: J2.12, U14.33 (MTDO/GPIO40/CLK_OUT2)
LCD_D2: J2.13, U14.34 (MTDI/GPIO41/CLK_OUT1)
LCD_D3: J2.14, U14.35 (MTMS/GPIO42)
LCD_D4: J2.15, U14.26 (*GPIO45)
LCD_D5: J2.16, U14.16 (*GPIO46)
LCD_D6: J2.17, U14.24 (GPIO47/SPICLK_P/SUBSPICLK_P_DIFF)
LCD_D7: J2.18, U14.25 (GPIO48/SPICLK_N/SUBSPICLK_N_DIFF)
LCD_DC: J2.7, U14.7 (GPIO7/TOUCH7/ADC1_CH6)
LCD_EN: U14.8 (GPIO15/U0RTS/ADC2_CH4/XTAL_32K_P)
LCD_RD: J2.9, U14.17 (GPIO9/TOUCH9/ADC1_CH8/FSPIHD/SUBSPIHD)
LCD_RES: J2.5, U14.5 (GPIO5/TOUCH5/ADC1_CH4)
LCD_WR: J2.8, U14.12 (GPIO8/TOUCH8/ADC1_CH7/SUBSPICS1)
LEDK1: J2.24, U15.6 (LED1)
LEDK2: J2.23, U15.5 (LED2)
LEDK3: J2.22, U15.4 (LED3)
LEDK4: J2.21, U15.3 (LED4)
unnamed: J1.A5 (CC1), R44.2
unnamed: J1.B5 (CC2), R46.2
unnamed: SW1.3 (NC), SW1.4 (NC)
unnamed: SW2.3 (NC), SW2.4 (NC)
PGOOD: R43.2, U14.19 (GPIO11/TOUCH11/ADC2_CH0/FSPID/FSPIIO5/S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)
PWR_EN: U14.18 (GPIO10/TOUCH10/ADC1_CH9/FSPICS0/FSPIIO4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)
RESET: U14.39 (GPIO1/TOUCH1/ADC1_CH0)
RX_3V3: U14.11 (GPIO18/U1RXD/ADC2_CH7/CLK_OUT3)
SCL: R47.2, U14.37 (U0TXD/GPIO43/CLK_OUT1)
SDA: R45.2, U14.36 (U0RXD/GPIO44/CLK_OUT2)
SMB_ALRT: U14.21 (GPIO13/TOUCH13/ADC2_CH2/FSPIQ/FSPIIO7/S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)
TP_INT: J2.29
TP_RESET: J2.26
TX_3V3: U14.10 (GPIO17/U1TXD/ADC2_CH6)
USB_D+: J1.A6 (D+), J1.B6 (D+), U14.14 (GPIO20/U1CTS/ADC2_CH9/CLK_OUT1/USB_D+)
USB_D-: J1.A7 (D-), J1.B7 (D-), U14.13 (GPIO19/U1RTS/ADC2_CH8/CLK_OUT2/USB_D-)

Notes on the sheet:
GPIO 36 and 37 are used for SPIRAM
