bitaxeorg/BitaxeGammaHex/fan.kicad_sch

## KiCad design fan.kicad_sch (2026-07-27)

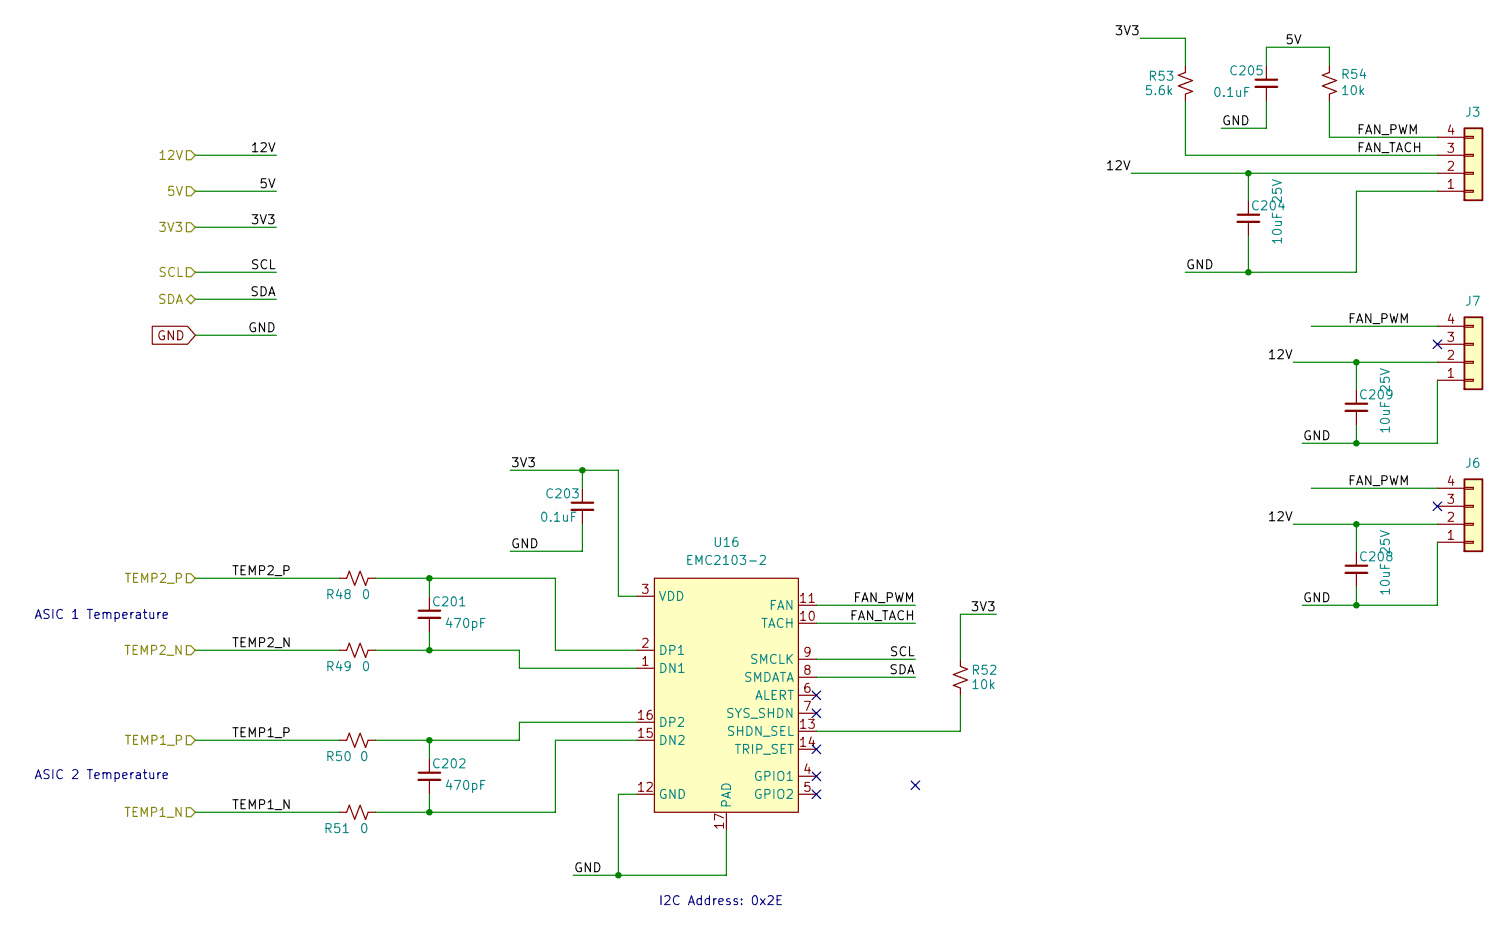
[picture p60: schematic fan.kicad_sch]

Parts:
C201, C202: 470pF; C_0402_1005Metric; PARTNO GRM1555C1H471JA01D
C203, C205: 0.1uF; C_0402_1005Metric; PARTNO KGM05AR71C104KH
C204, C208, C209: 10uF; C_0603_1608Metric; Voltage 25V; PARTNO GRM188R61E106KA73D
J3, J6, J7: Conn_01x04; 470531000; PARTNO 0470531000
R48, R49, R50, R51: 0; R_0402_1005Metric; PARTNO RC0402JR-070RL
R52, R54: 10k; R_0402_1005Metric; PARTNO RC0402DR-0710KL
R53: 5.6k; R_0402_1005Metric; PARTNO RC0402FR-075K6L
U16: EMC2103-2; QFN-16-1EP_4x4mm_P0.65mm_EP2.1x2.1mm; PARTNO EMC2103-4-AP-TR

Connections:
3V3: C203.1, R52.2, R53.2, U16.3 (VDD)
5V: C205.1, R54.2
12V: C204.1, C208.1, C209.1, J3.2, J6.2, J7.2
FAN_PWM: J3.4, J6.4, J7.4, R54.1, U16.11 (FAN)
FAN_TACH: J3.3, R53.1, U16.10 (TACH)
GND: C203.2, C204.2, C205.2, C208.2, C209.2, J3.1, J6.1, J7.1, U16.12 (GND), U16.17 (PAD)
unnamed: C201.1, R48.1, U16.2 (DP1)
unnamed: C201.2, R49.1, U16.1 (DN1)
unnamed: C202.1, R50.1, U16.16 (DP2)
unnamed: C202.2, R51.1, U16.15 (DN2)
unnamed: R52.1, U16.13 (SHDN_SEL)
SCL: U16.9 (SMCLK)
SDA: U16.8 (SMDATA)
TEMP1_N: R51.2
TEMP1_P: R50.2
TEMP2_N: R49.2
TEMP2_P: R48.2

Notes on the sheet:
I2C Address: 0x2E
ASIC 1 Temperature
ASIC 2 Temperature
