bitaxeorg/BitaxeGammaHex/level_shifter.kicad_sch

## KiCad design level_shifter.kicad_sch (2026-07-27)

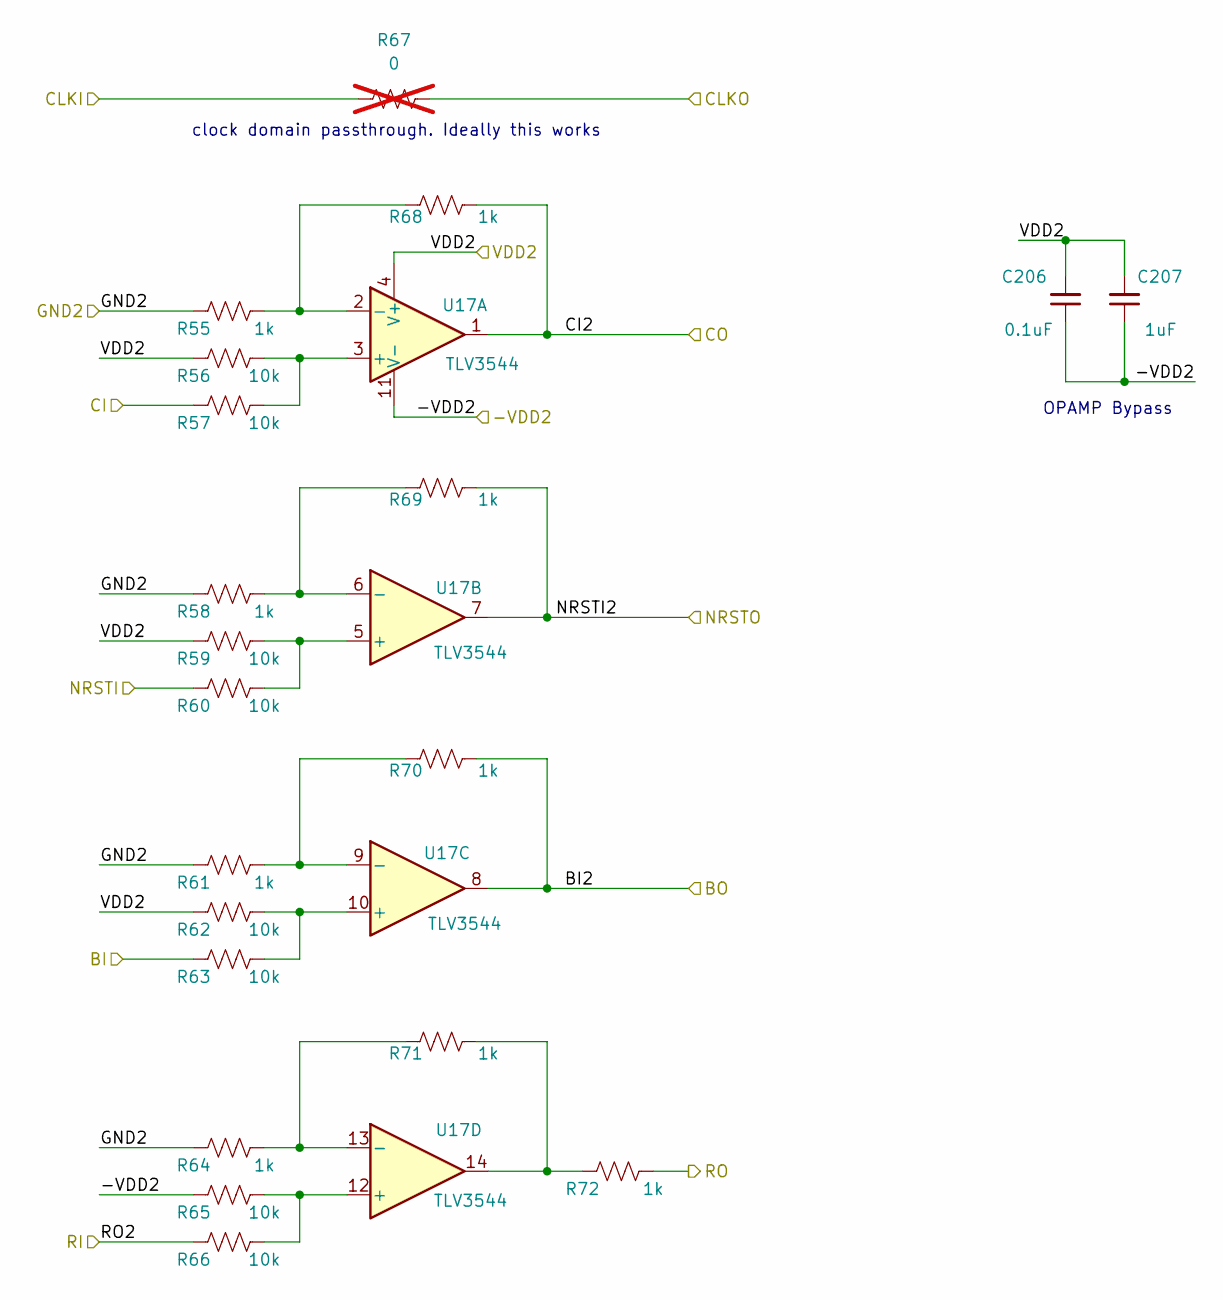
[picture p61: schematic level_shifter.kicad_sch]

Parts:
C206: 0.1uF; C_0402_1005Metric; PARTNO KGM05AR71C104KH
C207: 1uF; C_0402_1005Metric; PARTNO CL05A105KO5NNNC
R55, R58, R61, R64, R68, R69, R70, R71, R72: 1k; R_0402_1005Metric; PARTNO RC0402FR-071KL
R56, R57, R59, R60, R62, R63, R65, R66: 10k; R_0402_1005Metric; PARTNO RC0402DR-0710KL
R67: 0; R_0402_1005Metric; PARTNO RC0402JR-070RL; not fitted
U17: TLV3544; TSSOP-14_4.4x5mm_P0.65mm; PARTNO TLV3544IPWR

Connections:
-VDD2: C206.1, C207.1, R65.1, U17.11 (V-)
BI: R63.1
BI2: R70.1, U17.8
CI: R57.1
CI2: R68.1, U17.1
CLKI: R67.1
CLKO: R67.2
GND2: R55.2, R58.2, R61.2, R64.2
NRSTI: R60.1
NRSTI2: R69.1, U17.7
unnamed: R55.1, R68.2, U17.2 (-)
unnamed: R56.1, R57.2, U17.3 (+)
unnamed: R58.1, R69.2, U17.6 (-)
unnamed: R59.2, R60.2, U17.5 (+)
unnamed: R61.1, R70.2, U17.9 (-)
unnamed: R62.2, R63.2, U17.10 (+)
unnamed: R64.1, R71.2, U17.13 (-)
unnamed: R65.2, R66.2, U17.12 (+)
unnamed: R71.1, R72.2, U17.14
RI: R66.1
RO: R72.1
VDD2: C206.2, C207.2, R56.2, R59.1, R62.1, U17.4 (V+)

Notes on the sheet:
OPAMP Bypass
clock domain passthrough. Ideally this works
