bitaxeorg/BitaxeGammaHex/power.kicad_sch

## KiCad design power.kicad_sch (2026-07-27)

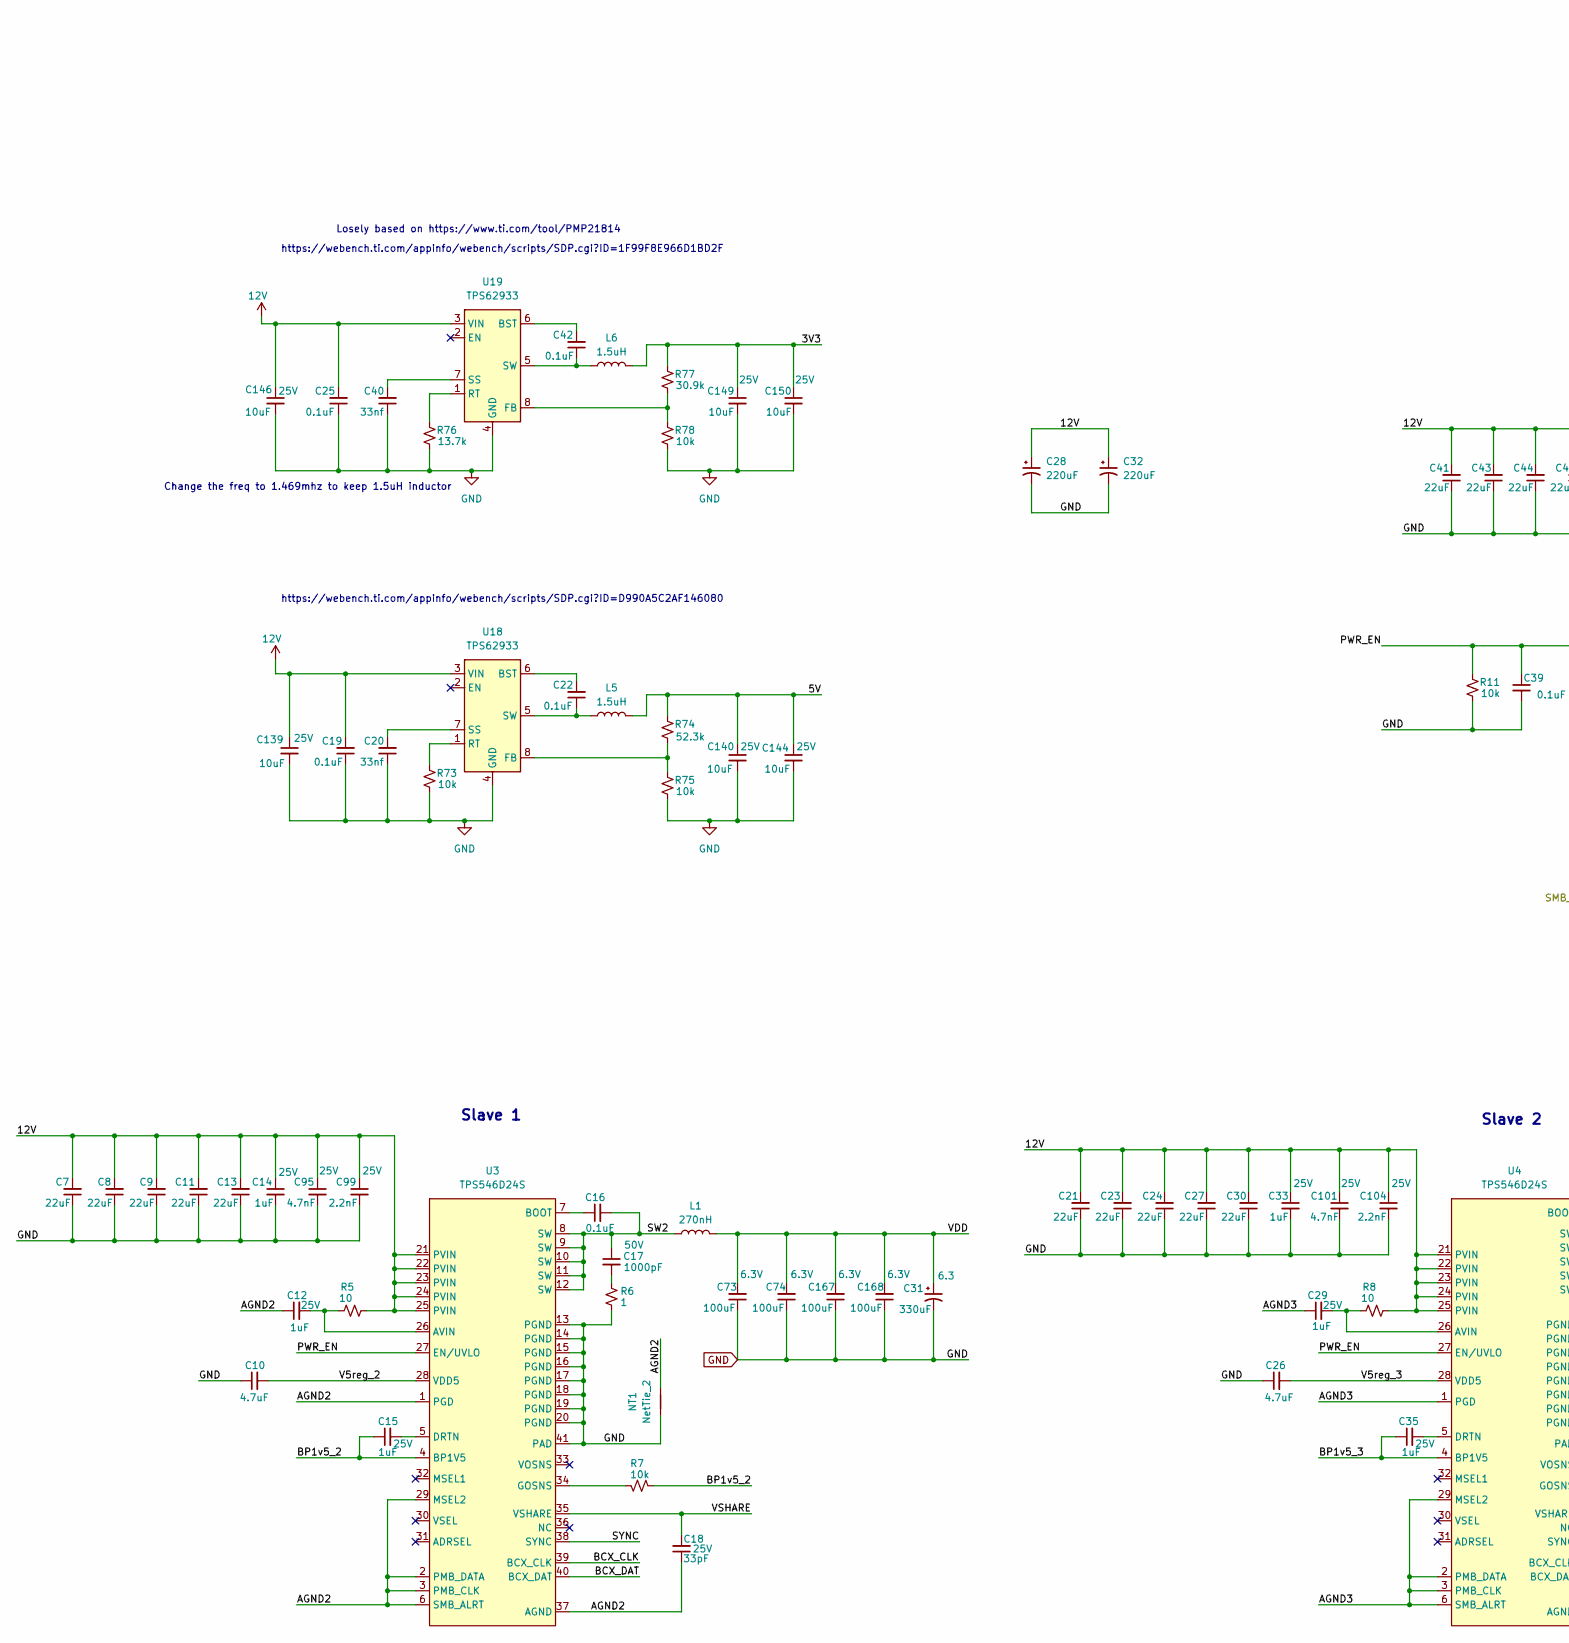
[picture p62: schematic power.kicad_sch, part in row 1, column 1]

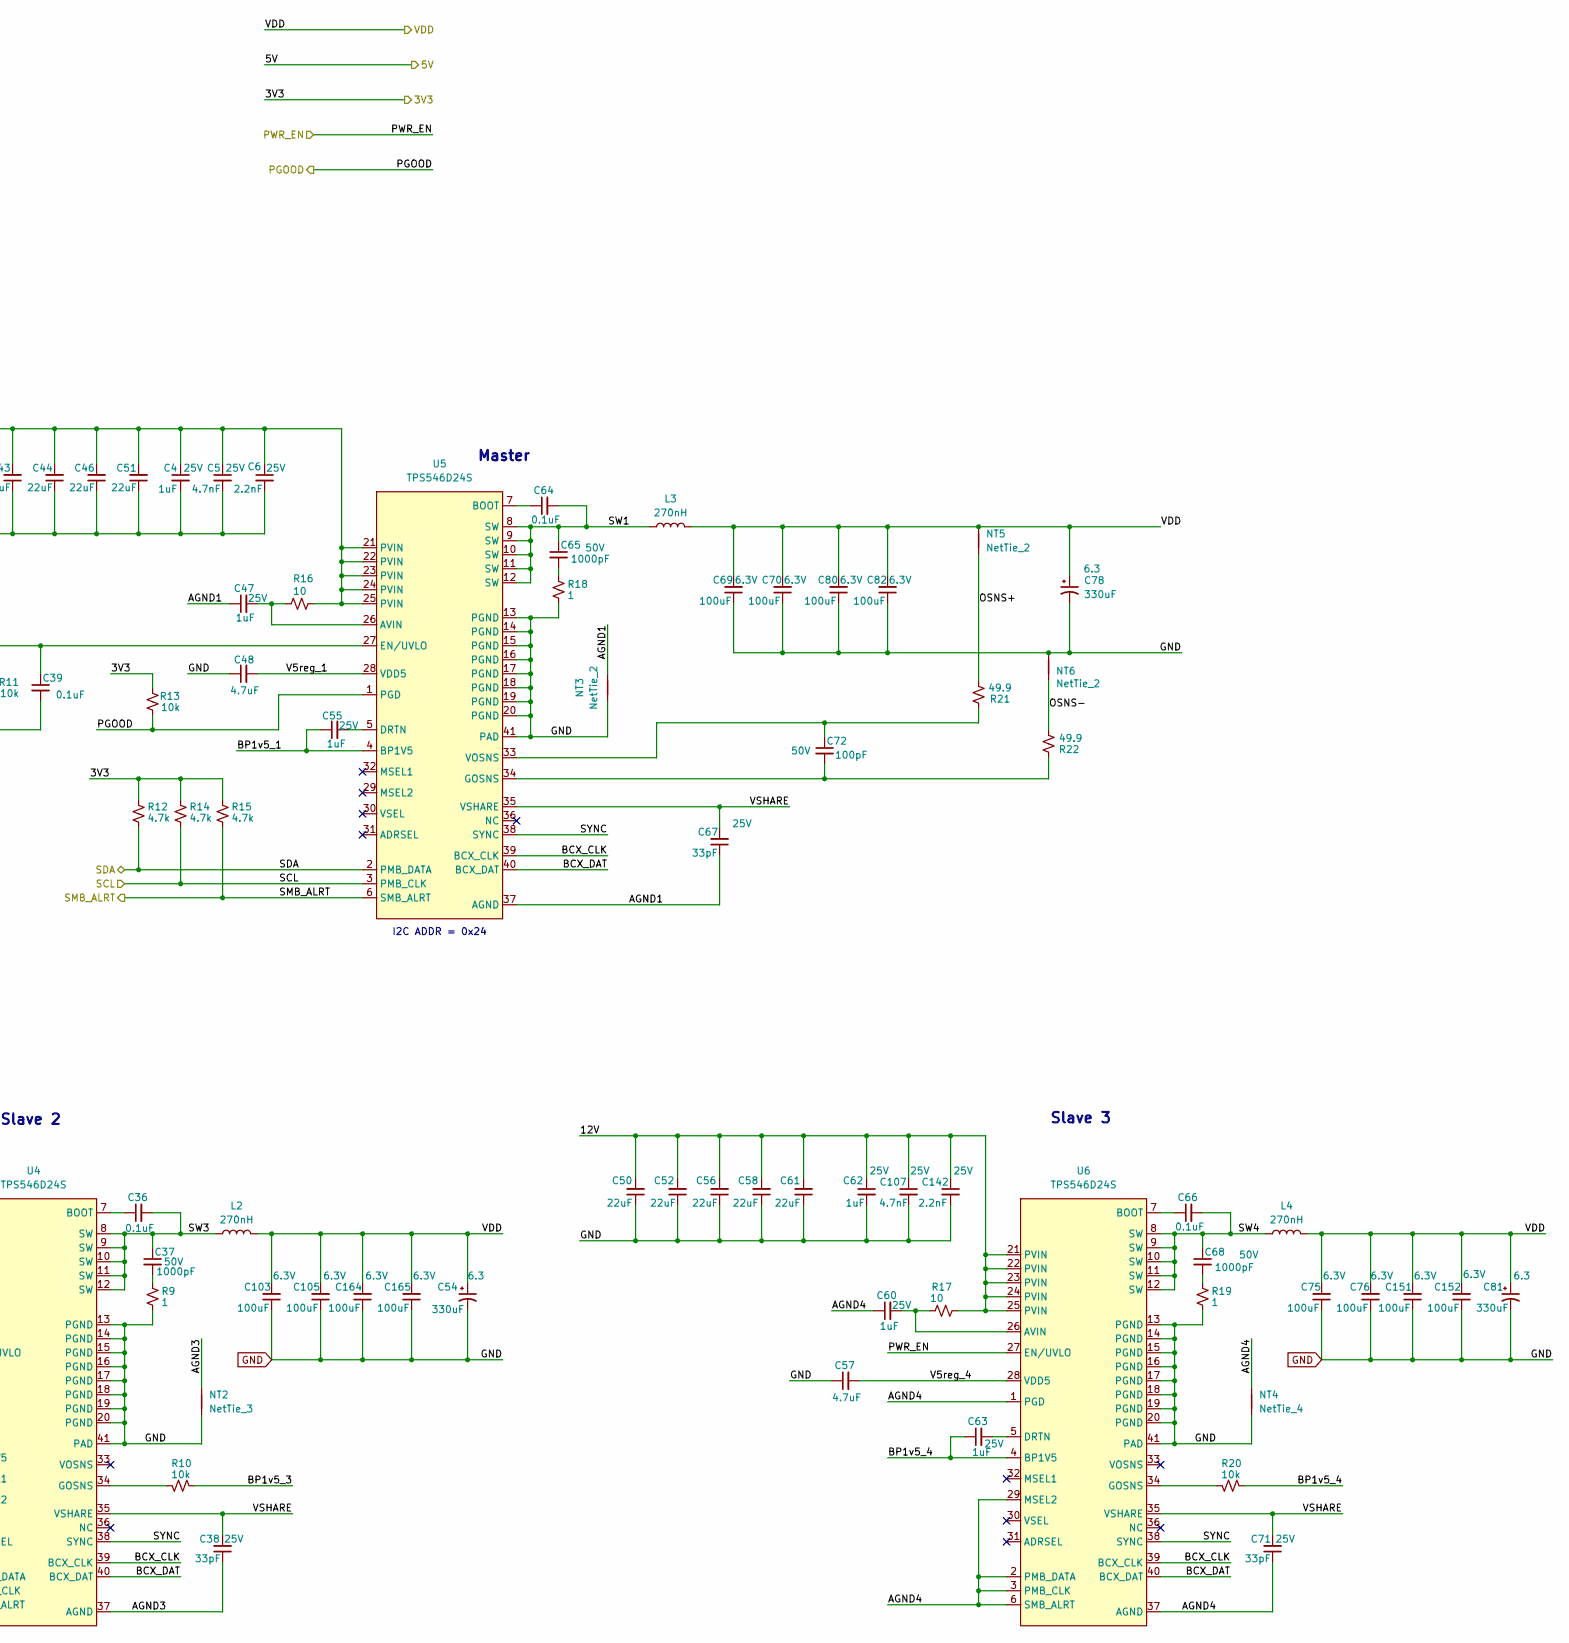
[picture p63: schematic power.kicad_sch, part in row 1, column 2]

Parts:
C4, C12, C14, C15, C29, C33, C35, C47, C55, C60, C62, C63: 1uF; C_0402_1005Metric; Voltage 25V; PARTNO CL05A105KO5NNNC
C5, C95, C101, C107: 4.7nF; C_0402_1005Metric; Voltage 25V; PARTNO GRM155R71E472KA01D
C6, C99, C104, C142: 2.2nF; C_0402_1005Metric; Voltage 25V; PARTNO GRM155R61H222KA01D
C7, C8, C9, C11, C13, C21, C23, C24, C27, C30, C41, C43, C44, C46, C50, C51, C52, C56, C58, C61: 22uF; C_0805_2012Metric; PARTNO CL21A226MAQNNNE
C10, C26, C48, C57: 4.7uF; C_0402_1005Metric; PARTNO GRM155R61A475MEAAD
C16, C36, C39, C64, C66: 0.1uF; C_0402_1005Metric; PARTNO KGM05AR71C104KH
C17, C37, C65, C68: 1000pF; C_0805_2012Metric; Voltage 50V; PARTNO CC0805KRX7R9BB102
C18, C38, C67, C71: 33pF; C_0402_1005Metric; Voltage 25V; PARTNO KGM05ACG1E330JH
C19, C22, C25, C42: 0.1uF; C_0402_1005Metric; PARTNO GRM188R61E106KA73D
C20, C40: 33nf; C_0402_1005Metric; PARTNO GCM155R71E333KA55D
C28, C32: 220uF; CP_Elec_8x10; PARTNO 118EC427
C31, C54, C78, C81: 330uF; CP_EIA-7343-15_Kemet-W; Voltage 6.3; PARTNO ECG-SY0J331R
C69, C70, C73, C74, C75, C76, C80, C82, C103, C105, C151, C152, C164, C165, C167, C168: 100uF; C_1206_3216Metric; Voltage 6.3V; PARTNO CL31A107MQHNNNE
C72: 100pF; C_0402_1005Metric; Voltage 50V; PARTNO CC0402JRNPO9BN101
C139, C140, C144, C146, C149, C150: 10uF; C_0603_1608Metric; Voltage 25V; PARTNO GRM188R61E106KA73D
L1, L2, L3, L4: 270nH; SLC1175-271MEC_COC; PARTNO SLC1175-121MEC
L5, L6: 1.5uH; L_Changjiang_FTC201612S; PARTNO FTC201612S1R5MBCA
NT1, NT3, NT5, NT6: NetTie_2; NetTie-2_SMD_Pad0.2mmx1mm
NT2: NetTie_3; NetTie-2_SMD_Pad0.2mmx1mm
NT4: NetTie_4; NetTie-2_SMD_Pad0.2mmx1mm
R5, R8, R16, R17: 10; R_0402_1005Metric; PARTNO RC0402FR-0710RL
R6, R9, R18, R19: 1; R_0805_2012Metric; PARTNO ESR10EZPJ1R0
R7, R10, R11, R13, R20, R73, R75, R78: 10k; R_0402_1005Metric; PARTNO RC0402DR-0710KL
R12, R14, R15: 4.7k; R_0402_1005Metric; PARTNO RC0402JR-074K7L
R21, R22: 49.9; R_0402_1005Metric; PARTNO RC0402FR-0749R9L
R74: 52.3k; R_0402_1005Metric; PARTNO RC0402FR-0752K3L
R76: 13.7k; R_0402_1005Metric; PARTNO RMCF0402FT13K7
R77: 30.9k; R_0402_1005Metric; PARTNO RC0402FR-0730K9L
U3, U4, U5, U6: TPS546D24S; LQFN40-CLIP; PARTNO TPS546D24SRVFR
U18, U19: TPS62933; SOT-583-8; PARTNO TPS62933DRLR

Connections:
3V3: C149.1, C150.1, L6.2, R12.1, R13.2, R14.1, R15.1, R77.2
5V: C140.1, C144.1, L5.2, R74.2
12V: C4.1, C5.1, C6.1, C7.2, C8.2, C9.2, C11.2, C13.2, C14.1, C19.2, C21.2, C23.2, C24.2, C25.2, C27.2, C28.1, C30.2, C32.1, C33.1, C41.2, C43.2, C44.2, C46.2, C50.2, C51.2, C52.2, C56.2, C58.2, C61.2, C62.1, C95.1, C99.1, C101.1, C104.1, C107.1, C139.1, C142.1, C146.1, R5.1, R8.1, R16.1, R17.1, U3.21 (PVIN), U3.22 (PVIN), U3.23 (PVIN), U3.24 (PVIN), U3.25 (PVIN), U4.21 (PVIN), U4.22 (PVIN), U4.23 (PVIN), U4.24 (PVIN), U4.25 (PVIN), U5.21 (PVIN), U5.22 (PVIN), U5.23 (PVIN), U5.24 (PVIN), U5.25 (PVIN), U6.21 (PVIN), U6.22 (PVIN), U6.23 (PVIN), U6.24 (PVIN), U6.25 (PVIN), U18.3 (VIN), U19.3 (VIN)
AGND1: C47.1, C67.1, NT3.2, U5.37 (AGND)
AGND2: C12.1, C18.1, NT1.2, U3.1 (PGD), U3.2 (PMB_DATA), U3.3 (PMB_CLK), U3.6 (SMB_ALRT), U3.29 (MSEL2), U3.37 (AGND)
AGND3: C29.1, C38.1, NT2.2, U4.1 (PGD), U4.2 (PMB_DATA), U4.3 (PMB_CLK), U4.6 (SMB_ALRT), U4.29 (MSEL2), U4.37 (AGND)
AGND4: C60.1, C71.1, NT4.2, U6.1 (PGD), U6.2 (PMB_DATA), U6.3 (PMB_CLK), U6.6 (SMB_ALRT), U6.29 (MSEL2), U6.37 (AGND)
BCX_CLK: U3.39 (BCX_CLK), U4.39 (BCX_CLK), U5.39 (BCX_CLK), U6.39 (BCX_CLK)
BCX_DAT: U3.40 (BCX_DAT), U4.40 (BCX_DAT), U5.40 (BCX_DAT), U6.40 (BCX_DAT)
BP1v5_1: C55.1, U5.4 (BP1V5)
BP1v5_2: C15.1, R7.1, U3.4 (BP1V5)
BP1v5_3: C35.1, R10.1, U4.4 (BP1V5)
BP1v5_4: C63.1, R20.1, U6.4 (BP1V5)
GND: C4.2, C5.2, C6.2, C7.1, C8.1, C9.1, C10.1, C11.1, C13.1, C14.2, C19.1, C20.1, C21.1, C23.1, C24.1, C25.1, C26.1, C27.1, C28.2, C30.1, C31.2, C32.2, C33.2, C39.2, C40.1, C41.1, C43.1, C44.1, C46.1, C48.1, C50.1, C51.1, C52.1, C54.2, C56.1, C57.1, C58.1, C61.1, C62.2, C69.1, C70.1, C73.1, C74.1, C75.1, C76.1, C78.2, C80.1, C81.2, C82.1, C95.2, C99.2, C101.2, C103.1, C104.2, C105.1, C107.2, C139.2, C140.2, C142.2, C144.2, C146.2, C149.2, C150.2, C151.1, C152.1, C164.1, C165.1, C167.1, C168.1, NT1.1, NT2.1, NT3.1, NT4.1, NT6.2, R6.2, R9.2, R11.1, R18.2, R19.2, R73.1, R75.1, R76.1, R78.1, U3.13 (PGND), U3.14 (PGND), U3.15 (PGND), U3.16 (PGND), U3.17 (PGND), U3.18 (PGND), U3.19 (PGND), U3.20 (PGND), U3.41 (PAD), U4.13 (PGND), U4.14 (PGND), U4.15 (PGND), U4.16 (PGND), U4.17 (PGND), U4.18 (PGND), U4.19 (PGND), U4.20 (PGND), U4.41 (PAD), U5.13 (PGND), U5.14 (PGND), U5.15 (PGND), U5.16 (PGND), U5.17 (PGND), U5.18 (PGND), U5.19 (PGND), U5.20 (PGND), U5.41 (PAD), U6.13 (PGND), U6.14 (PGND), U6.15 (PGND), U6.16 (PGND), U6.17 (PGND), U6.18 (PGND), U6.19 (PGND), U6.20 (PGND), U6.41 (PAD), U18.4 (GND), U19.4 (GND)
unnamed: C12.2, R5.2, U3.26 (AVIN)
unnamed: C15.2, U3.5 (DRTN)
unnamed: C16.1, U3.7 (BOOT)
unnamed: C17.2, R6.1
unnamed: C20.2, U18.7 (SS)
unnamed: C22.1, L5.1, U18.5 (SW)
unnamed: C22.2, U18.6 (BST)
unnamed: C29.2, R8.2, U4.26 (AVIN)
unnamed: C35.2, U4.5 (DRTN)
unnamed: C36.1, U4.7 (BOOT)
unnamed: C37.2, R9.1
unnamed: C40.2, U19.7 (SS)
unnamed: C42.1, L6.1, U19.5 (SW)
unnamed: C42.2, U19.6 (BST)
unnamed: C47.2, R16.2, U5.26 (AVIN)
unnamed: C55.2, U5.5 (DRTN)
unnamed: C60.2, R17.2, U6.26 (AVIN)
unnamed: C63.2, U6.5 (DRTN)
unnamed: C64.1, U5.7 (BOOT)
unnamed: C65.2, R18.1
unnamed: C66.1, U6.7 (BOOT)
unnamed: C68.2, R19.1
unnamed: C72.1, R21.1, U5.33 (VOSNS)
unnamed: C72.2, R22.2, U5.34 (GOSNS)
unnamed: R7.2, U3.34 (GOSNS)
unnamed: R10.2, U4.34 (GOSNS)
unnamed: R20.2, U6.34 (GOSNS)
unnamed: R73.2, U18.1 (RT)
unnamed: R74.1, R75.2, U18.8 (FB)
unnamed: R76.2, U19.1 (RT)
unnamed: R77.1, R78.2, U19.8 (FB)
OSNS+: NT5.1, R21.2
OSNS-: NT6.1, R22.1
PGOOD: R13.1, U5.1 (PGD)
PWR_EN: C39.1, R11.2, U3.27 (EN/UVLO), U4.27 (EN/UVLO), U5.27 (EN/UVLO), U6.27 (EN/UVLO)
SCL: R14.2, U5.3 (PMB_CLK)
SDA: R12.2, U5.2 (PMB_DATA)
SMB_ALRT: R15.2, U5.6 (SMB_ALRT)
SW1: C64.2, C65.1, L3.1, U5.8 (SW), U5.9 (SW), U5.10 (SW), U5.11 (SW), U5.12 (SW)
SW2: C16.2, C17.1, L1.1, U3.8 (SW), U3.9 (SW), U3.10 (SW), U3.11 (SW), U3.12 (SW)
SW3: C36.2, C37.1, L2.1, U4.8 (SW), U4.9 (SW), U4.10 (SW), U4.11 (SW), U4.12 (SW)
SW4: C66.2, C68.1, L4.1, U6.8 (SW), U6.9 (SW), U6.10 (SW), U6.11 (SW), U6.12 (SW)
SYNC: U3.38 (SYNC), U4.38 (SYNC), U5.38 (SYNC), U6.38 (SYNC)
V5reg_1: C48.2, U5.28 (VDD5)
V5reg_2: C10.2, U3.28 (VDD5)
V5reg_3: C26.2, U4.28 (VDD5)
V5reg_4: C57.2, U6.28 (VDD5)
VDD: C31.1, C54.1, C69.2, C70.2, C73.2, C74.2, C75.2, C76.2, C78.1, C80.2, C81.1, C82.2, C103.2, C105.2, C151.2, C152.2, C164.2, C165.2, C167.2, C168.2, L1.2, L2.2, L3.2, L4.2, NT5.2
VSHARE: C18.2, C38.2, C67.2, C71.2, U3.35 (VSHARE), U4.35 (VSHARE), U5.35 (VSHARE), U6.35 (VSHARE)

Notes on the sheet:
I2C ADDR = 0x24
Slave 1
Change the freq to 1.469mhz to keep 1.5uH inductor
https://webench.ti.com/appinfo/webench/scripts/SDP.cgi?ID=D990A5C2AF146080
https://webench.ti.com/appinfo/webench/scripts/SDP.cgi?ID=1F99F8E966D1BD2F
Slave 3
Losely based on https://www.ti.com/tool/PMP21814
Master
Slave 2
