bitaxeorg/BitaxeGammaHex/untitled.kicad_sch

## KiCad design untitled.kicad_sch (2026-07-20)

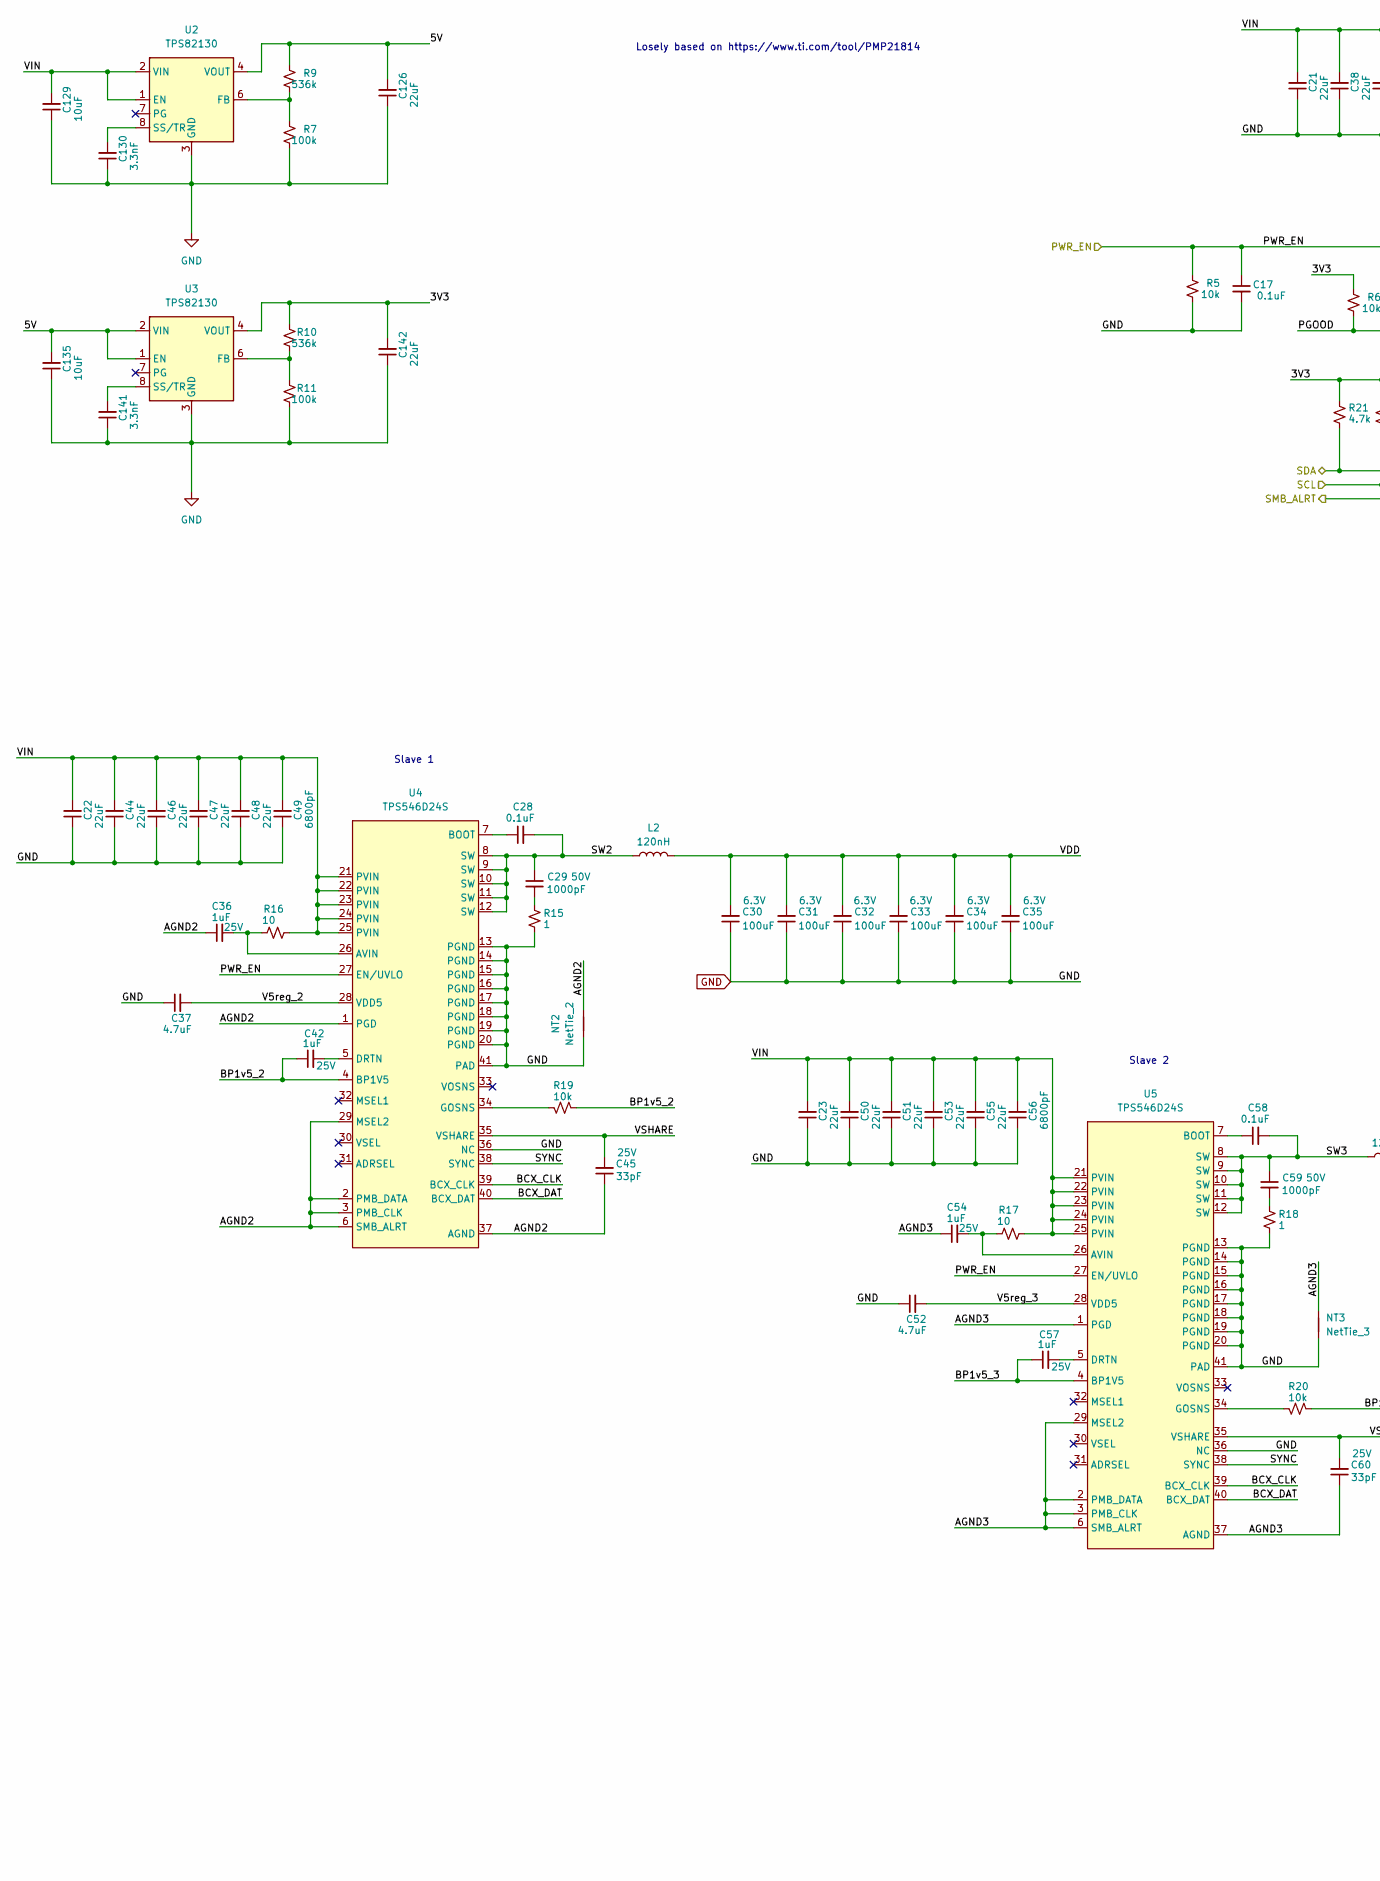
[picture p64: schematic untitled.kicad_sch, part in row 1, column 1]

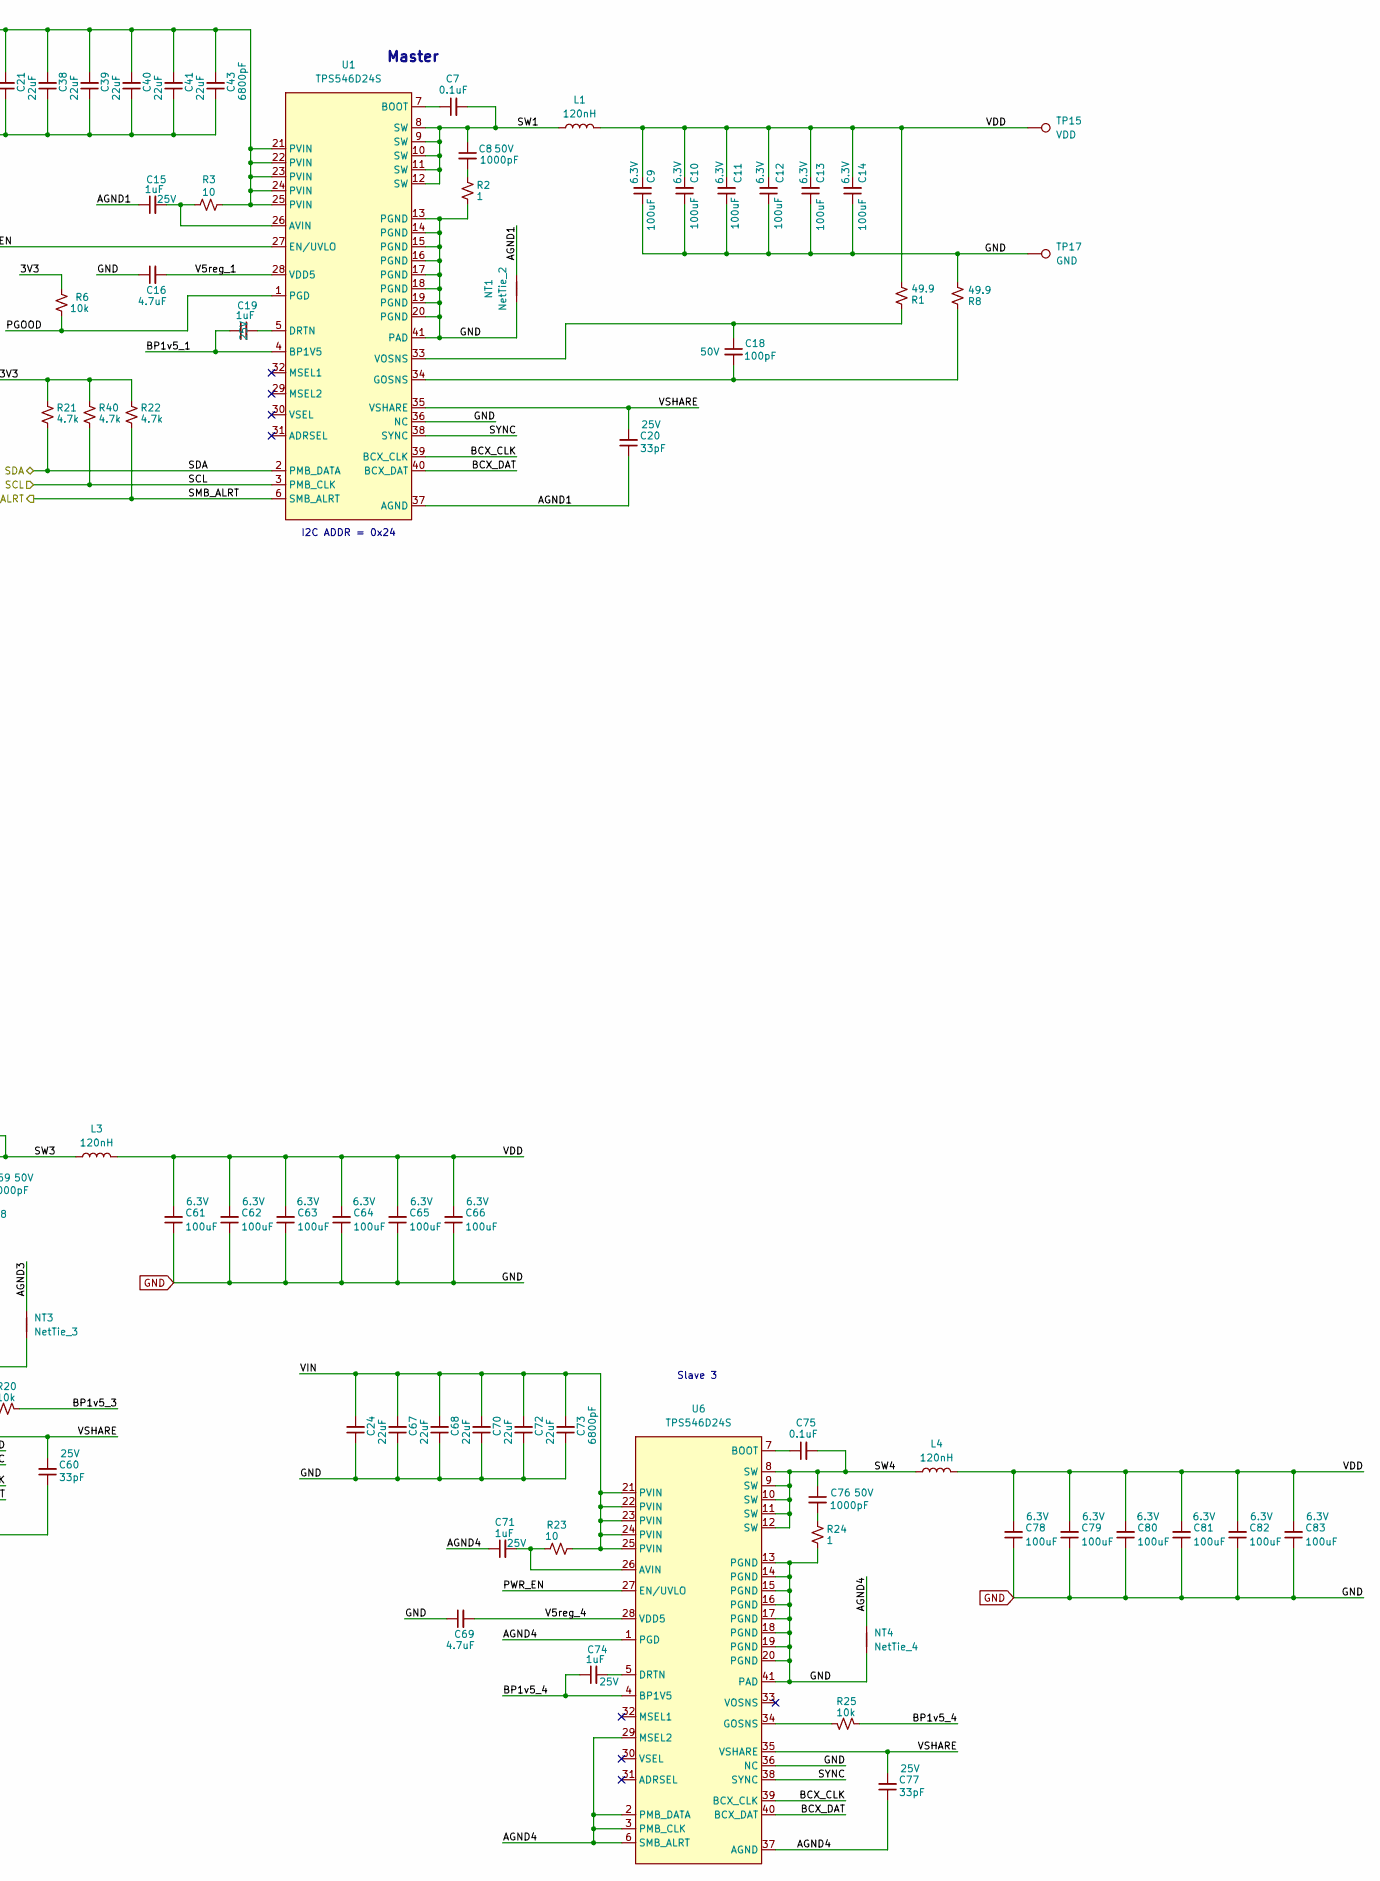
[picture p65: schematic untitled.kicad_sch, part in row 1, column 2]

Parts:
C7, C17, C28, C58, C75: 0.1uF; C_0402_1005Metric; PARTNO KGM05AR71C104KH
C8, C29, C59, C76: 1000pF; C_0805_2012Metric; Voltage 50V; PARTNO CC0805KRX7R9BB102
C9, C10, C11, C12, C13, C14, C30, C31, C32, C33, C34, C35, C61, C62, C63, C64, C65, C66, C78, C79, C80, C81, C82, C83: 100uF; C_1206_3216Metric; Voltage 6.3V; PARTNO CL31A107MQHNNNE
C15, C19, C36, C42, C54, C57, C71, C74: 1uF; C_0402_1005Metric; Voltage 25V; PARTNO TMK107B7105KA-T
C16, C37, C52, C69: 4.7uF; C_0402_1005Metric; PARTNO GRM155R61A475MEAAD
C18: 100pF; C_0402_1005Metric; Voltage 50V; PARTNO CC0402JRNPO9BN101
C20, C45, C60, C77: 33pF; C_0402_1005Metric; Voltage 25V; PARTNO KGM05ACG1E330JH
C21, C22, C23, C24, C38, C39, C40, C41, C44, C46, C47, C48, C50, C51, C53, C55, C67, C68, C70, C72, C126, C142: 22uF; C_0805_2012Metric
C43, C49, C56, C73: 6800pF; C_0402_1005Metric
C129, C135: 10uF; C_0805_2012Metric
C130, C141: 3.3nF; C_0402_1005Metric
L1, L2, L3, L4: 120nH; SLC1175-271MEC_COC; PARTNO SLC1175-121MEC
NT1, NT2: NetTie_2; NetTie-2_SMD_Pad0.2mmx1mm
NT3: NetTie_3; NetTie-2_SMD_Pad0.2mmx1mm
NT4: NetTie_4; NetTie-2_SMD_Pad0.2mmx1mm
R1, R8: 49.9; R_0402_1005Metric; PARTNO RC0402FR-0749R9L
R2, R15, R18, R24: 1; R_0805_2012Metric; PARTNO ESR10EZPJ1R0
R3, R16, R17, R23: 10; R_0402_1005Metric; PARTNO RC0402FR-0710RL
R5, R6, R19, R20, R25: 10k; R_0402_1005Metric; PARTNO RC0402JR-0710KL
R7, R11: 100k; R_0402_1005Metric
R9, R10: 536k; R_0402_1005Metric
R21, R22, R40: 4.7k; R_0402_1005Metric; PARTNO RC0402JR-074K7L
TP15: VDD; TestPoint_Pad_D1.0mm
TP17: GND; TestPoint_Pad_D1.0mm
U1, U4, U5, U6: TPS546D24S; LQFN40-CLIP; PARTNO TPS546D24SRVFR
U2, U3: TPS82130; Texas_SIL0008D_MicroSiP-8-1EP_2.8x3mm_P0.65mm_EP1.1x1.9mm_T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

Connections:
3V3: C142.2, R6.2, R10.2, R21.1, R22.1, R40.1, U3.4 (VOUT), U3.5 (VOUT)
5V: C126.2, C135.2, R9.2, U2.4 (VOUT), U2.5 (VOUT), U3.1 (EN), U3.2 (VIN)
AGND1: C15.1, C20.1, NT1.2, U1.37 (AGND)
AGND2: C36.1, C45.1, NT2.2, U4.1 (PGD), U4.2 (PMB_DATA), U4.3 (PMB_CLK), U4.6 (SMB_ALRT), U4.29 (MSEL2), U4.37 (AGND)
AGND3: C54.1, C60.1, NT3.2, U5.1 (PGD), U5.2 (PMB_DATA), U5.3 (PMB_CLK), U5.6 (SMB_ALRT), U5.29 (MSEL2), U5.37 (AGND)
AGND4: C71.1, C77.1, NT4.2, U6.1 (PGD), U6.2 (PMB_DATA), U6.3 (PMB_CLK), U6.6 (SMB_ALRT), U6.29 (MSEL2), U6.37 (AGND)
BCX_CLK: U1.39 (BCX_CLK), U4.39 (BCX_CLK), U5.39 (BCX_CLK), U6.39 (BCX_CLK)
BCX_DAT: U1.40 (BCX_DAT), U4.40 (BCX_DAT), U5.40 (BCX_DAT), U6.40 (BCX_DAT)
BP1v5_1: C19.1, U1.4 (BP1V5)
BP1v5_2: C42.1, R19.1, U4.4 (BP1V5)
BP1v5_3: C57.1, R20.1, U5.4 (BP1V5)
BP1v5_4: C74.1, R25.1, U6.4 (BP1V5)
GND: C9.1, C10.1, C11.1, C12.1, C13.1, C14.1, C16.1, C17.2, C21.1, C22.1, C23.1, C24.1, C30.1, C31.1, C32.1, C33.1, C34.1, C35.1, C37.1, C38.1, C39.1, C40.1, C41.1, C43.1, C44.1, C46.1, C47.1, C48.1, C49.1, C50.1, C51.1, C52.1, C53.1, C55.1, C56.1, C61.1, C62.1, C63.1, C64.1, C65.1, C66.1, C67.1, C68.1, C69.1, C70.1, C72.1, C73.1, C78.1, C79.1, C80.1, C81.1, C82.1, C83.1, C126.1, C129.1, C130.1, C135.1, C141.1, C142.1, NT1.1, NT2.1, NT3.1, NT4.1, R2.2, R5.1, R7.1, R8.1, R11.1, R15.2, R18.2, R24.2, TP17.1, U1.13 (PGND), U1.14 (PGND), U1.15 (PGND), U1.16 (PGND), U1.17 (PGND), U1.18 (PGND), U1.19 (PGND), U1.20 (PGND), U1.36 (NC), U1.41 (PAD), U2.3 (GND), U2.9 (GND), U3.3 (GND), U3.9 (GND), U4.13 (PGND), U4.14 (PGND), U4.15 (PGND), U4.16 (PGND), U4.17 (PGND), U4.18 (PGND), U4.19 (PGND), U4.20 (PGND), U4.36 (NC), U4.41 (PAD), U5.13 (PGND), U5.14 (PGND), U5.15 (PGND), U5.16 (PGND), U5.17 (PGND), U5.18 (PGND), U5.19 (PGND), U5.20 (PGND), U5.36 (NC), U5.41 (PAD), U6.13 (PGND), U6.14 (PGND), U6.15 (PGND), U6.16 (PGND), U6.17 (PGND), U6.18 (PGND), U6.19 (PGND), U6.20 (PGND), U6.36 (NC), U6.41 (PAD)
unnamed: C7.1, U1.7 (BOOT)
unnamed: C8.2, R2.1
unnamed: C15.2, R3.2, U1.26 (AVIN)
unnamed: C18.1, R1.1, U1.33 (VOSNS)
unnamed: C18.2, R8.2, U1.34 (GOSNS)
unnamed: C19.2, U1.5 (DRTN)
unnamed: C28.1, U4.7 (BOOT)
unnamed: C29.2, R15.1
unnamed: C36.2, R16.2, U4.26 (AVIN)
unnamed: C42.2, U4.5 (DRTN)
unnamed: C54.2, R17.2, U5.26 (AVIN)
unnamed: C57.2, U5.5 (DRTN)
unnamed: C58.1, U5.7 (BOOT)
unnamed: C59.2, R18.1
unnamed: C71.2, R23.2, U6.26 (AVIN)
unnamed: C74.2, U6.5 (DRTN)
unnamed: C75.1, U6.7 (BOOT)
unnamed: C76.2, R24.1
unnamed: C130.2, U2.8 (SS/TR)
unnamed: C141.2, U3.8 (SS/TR)
unnamed: R7.2, R9.1, U2.6 (FB)
unnamed: R10.1, R11.2, U3.6 (FB)
unnamed: R19.2, U4.34 (GOSNS)
unnamed: R20.2, U5.34 (GOSNS)
unnamed: R25.2, U6.34 (GOSNS)
PGOOD: R6.1, U1.1 (PGD)
PWR_EN: C17.1, R5.2, U1.27 (EN/UVLO), U4.27 (EN/UVLO), U5.27 (EN/UVLO), U6.27 (EN/UVLO)
SCL: R40.2, U1.3 (PMB_CLK)
SDA: R21.2, U1.2 (PMB_DATA)
SMB_ALRT: R22.2, U1.6 (SMB_ALRT)
SW1: C7.2, C8.1, L1.1, U1.8 (SW), U1.9 (SW), U1.10 (SW), U1.11 (SW), U1.12 (SW)
SW2: C28.2, C29.1, L2.1, U4.8 (SW), U4.9 (SW), U4.10 (SW), U4.11 (SW), U4.12 (SW)
SW3: C58.2, C59.1, L3.1, U5.8 (SW), U5.9 (SW), U5.10 (SW), U5.11 (SW), U5.12 (SW)
SW4: C75.2, C76.1, L4.1, U6.8 (SW), U6.9 (SW), U6.10 (SW), U6.11 (SW), U6.12 (SW)
SYNC: U1.38 (SYNC), U4.38 (SYNC), U5.38 (SYNC), U6.38 (SYNC)
V5reg_1: C16.2, U1.28 (VDD5)
V5reg_2: C37.2, U4.28 (VDD5)
V5reg_3: C52.2, U5.28 (VDD5)
V5reg_4: C69.2, U6.28 (VDD5)
VDD: C9.2, C10.2, C11.2, C12.2, C13.2, C14.2, C30.2, C31.2, C32.2, C33.2, C34.2, C35.2, C61.2, C62.2, C63.2, C64.2, C65.2, C66.2, C78.2, C79.2, C80.2, C81.2, C82.2, C83.2, L1.2, L2.2, L3.2, L4.2, R1.2, TP15.1
VIN: C21.2, C22.2, C23.2, C24.2, C38.2, C39.2, C40.2, C41.2, C43.2, C44.2, C46.2, C47.2, C48.2, C49.2, C50.2, C51.2, C53.2, C55.2, C56.2, C67.2, C68.2, C70.2, C72.2, C73.2, C129.2, R3.1, R16.1, R17.1, R23.1, U1.21 (PVIN), U1.22 (PVIN), U1.23 (PVIN), U1.24 (PVIN), U1.25 (PVIN), U2.1 (EN), U2.2 (VIN), U4.21 (PVIN), U4.22 (PVIN), U4.23 (PVIN), U4.24 (PVIN), U4.25 (PVIN), U5.21 (PVIN), U5.22 (PVIN), U5.23 (PVIN), U5.24 (PVIN), U5.25 (PVIN), U6.21 (PVIN), U6.22 (PVIN), U6.23 (PVIN), U6.24 (PVIN), U6.25 (PVIN)
VSHARE: C20.2, C45.2, C60.2, C77.2, U1.35 (VSHARE), U4.35 (VSHARE), U5.35 (VSHARE), U6.35 (VSHARE)

Notes on the sheet:
I2C ADDR = 0x24
Slave 3
Slave 2
Slave 1
Losely based on https://www.ti.com/tool/PMP21814
Master
